rimelq/VISTAF-RoboSkin-Vision-Integrated-Multimodal-Sensor/Multimodal_Sensor/Demos_report/FINAL_E_deformed/combined_outputs/temp_temperature_legend_horizontal.png

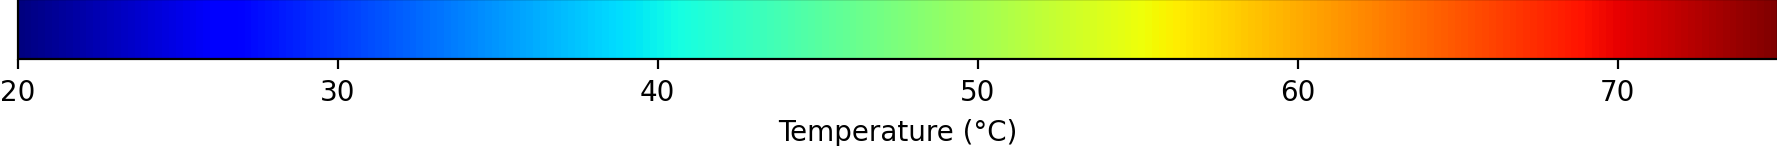
Multimodal_Sensor/Demos_report/FINAL_E_deformed/combined_outputs/temp_temperature_legend_horizontal.png
