rimelq/VISTAF-RoboSkin-Vision-Integrated-Multimodal-Sensor/Multimodal_Sensor/Demos_report/FINAL_E_deformed/force_sensing/ftp_run/03_ref_def_crops_with_roi.png

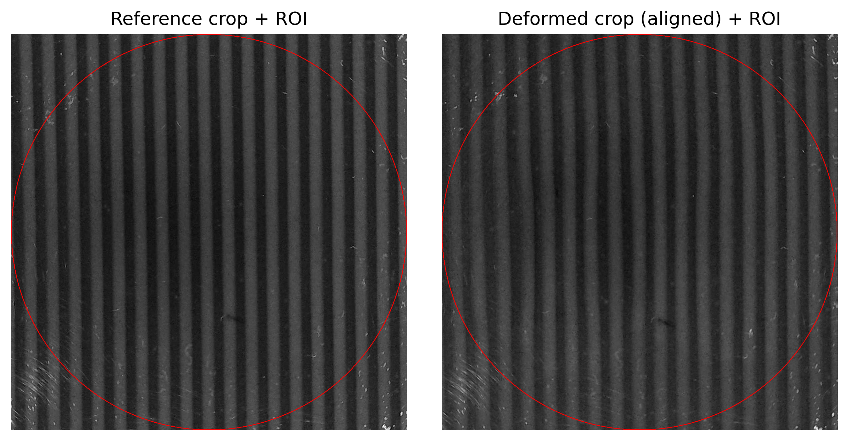
Multimodal_Sensor/Demos_report/FINAL_E_deformed/force_sensing/ftp_run/03_ref_def_crops_with_roi.png
