rimelq/VISTAF-RoboSkin-Vision-Integrated-Multimodal-Sensor/Multimodal_Sensor/Demos_report/FINAL_E_deformed/temperature_sensing/mask_color_support.png

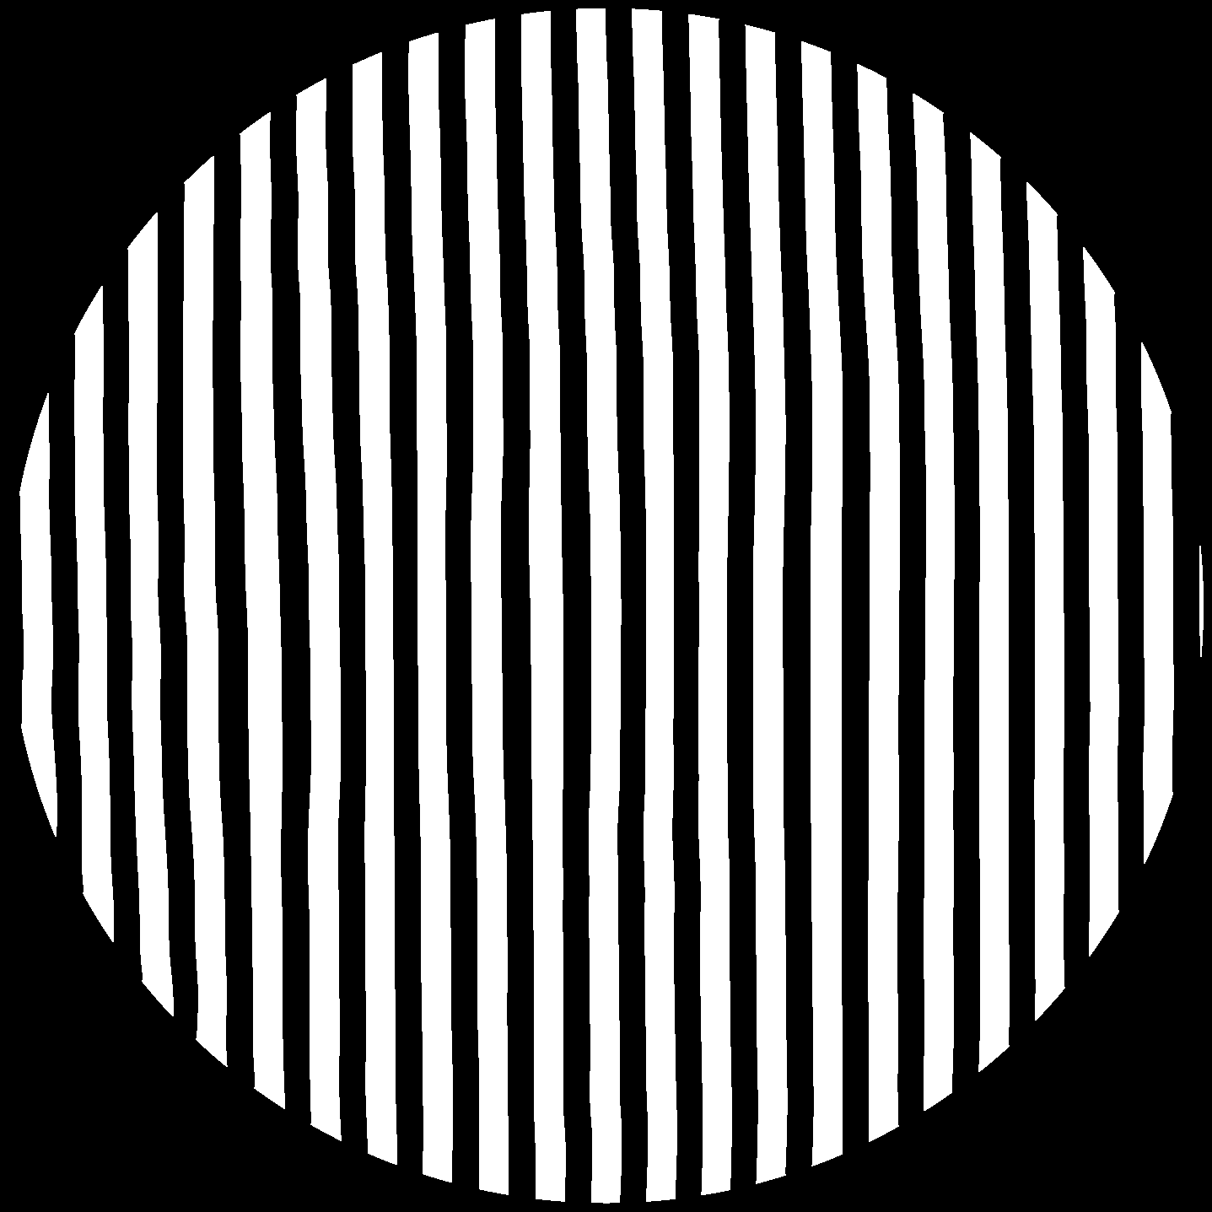
Multimodal_Sensor/Demos_report/FINAL_E_deformed/temperature_sensing/mask_color_support.png
