rimelq/VISTAF-RoboSkin-Vision-Integrated-Multimodal-Sensor/Multimodal_Sensor/Demos_report/FINAL_E_deformed/temperature_sensing/mask_roi.png

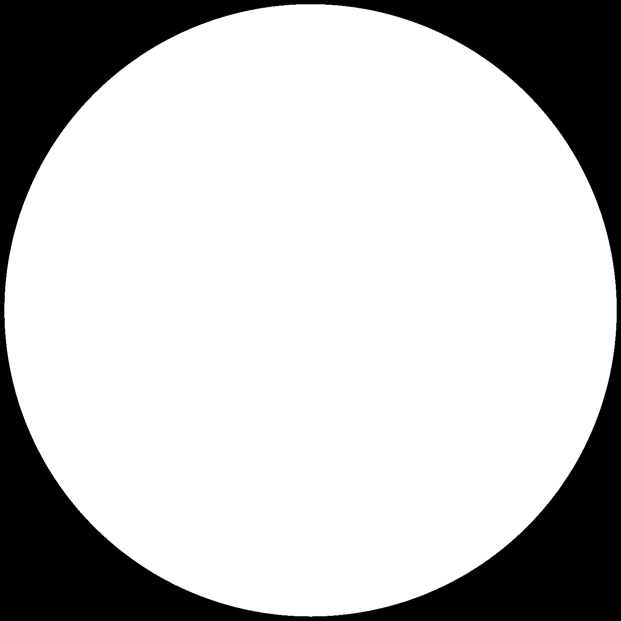
Multimodal_Sensor/Demos_report/FINAL_E_deformed/temperature_sensing/mask_roi.png
