rimelq/VISTAF-RoboSkin-Vision-Integrated-Multimodal-Sensor/Multimodal_Sensor/Demos_report/FINAL_F_deformed/force_sensing/ftp_run/07_phase_and_height_FINAL_SMOOTH_ROI.png

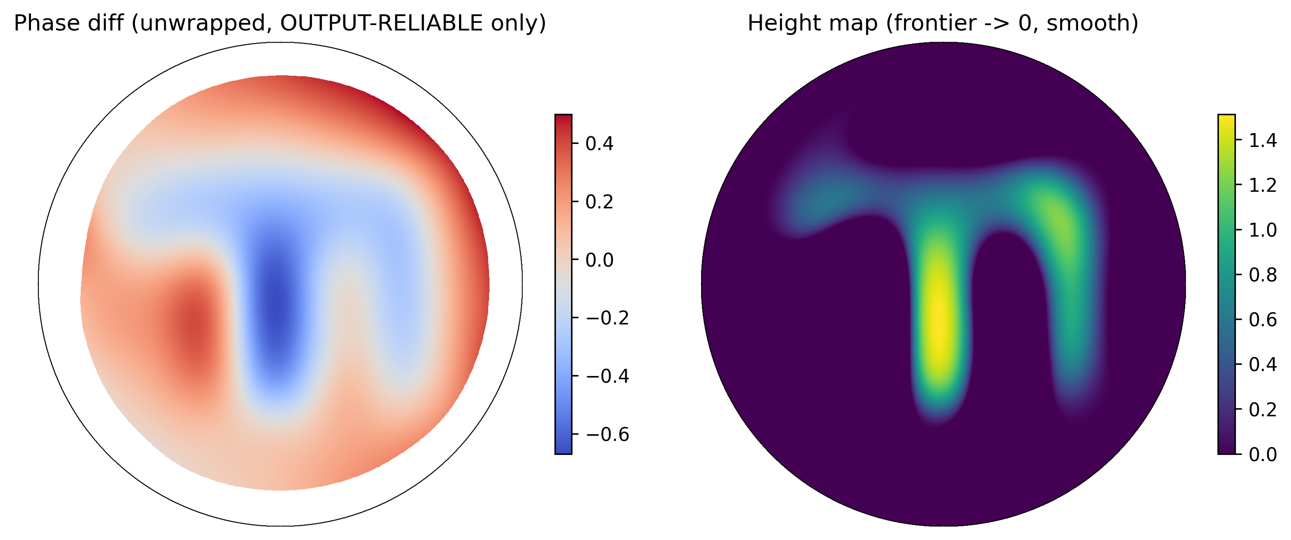
Multimodal_Sensor/Demos_report/FINAL_F_deformed/force_sensing/ftp_run/07_phase_and_height_FINAL_SMOOTH_ROI.png
