rimelq/VISTAF-RoboSkin-Vision-Integrated-Multimodal-Sensor/Multimodal_Sensor/Demos_report/FINAL_P_deformed/temperature_sensing/mask_dark.png

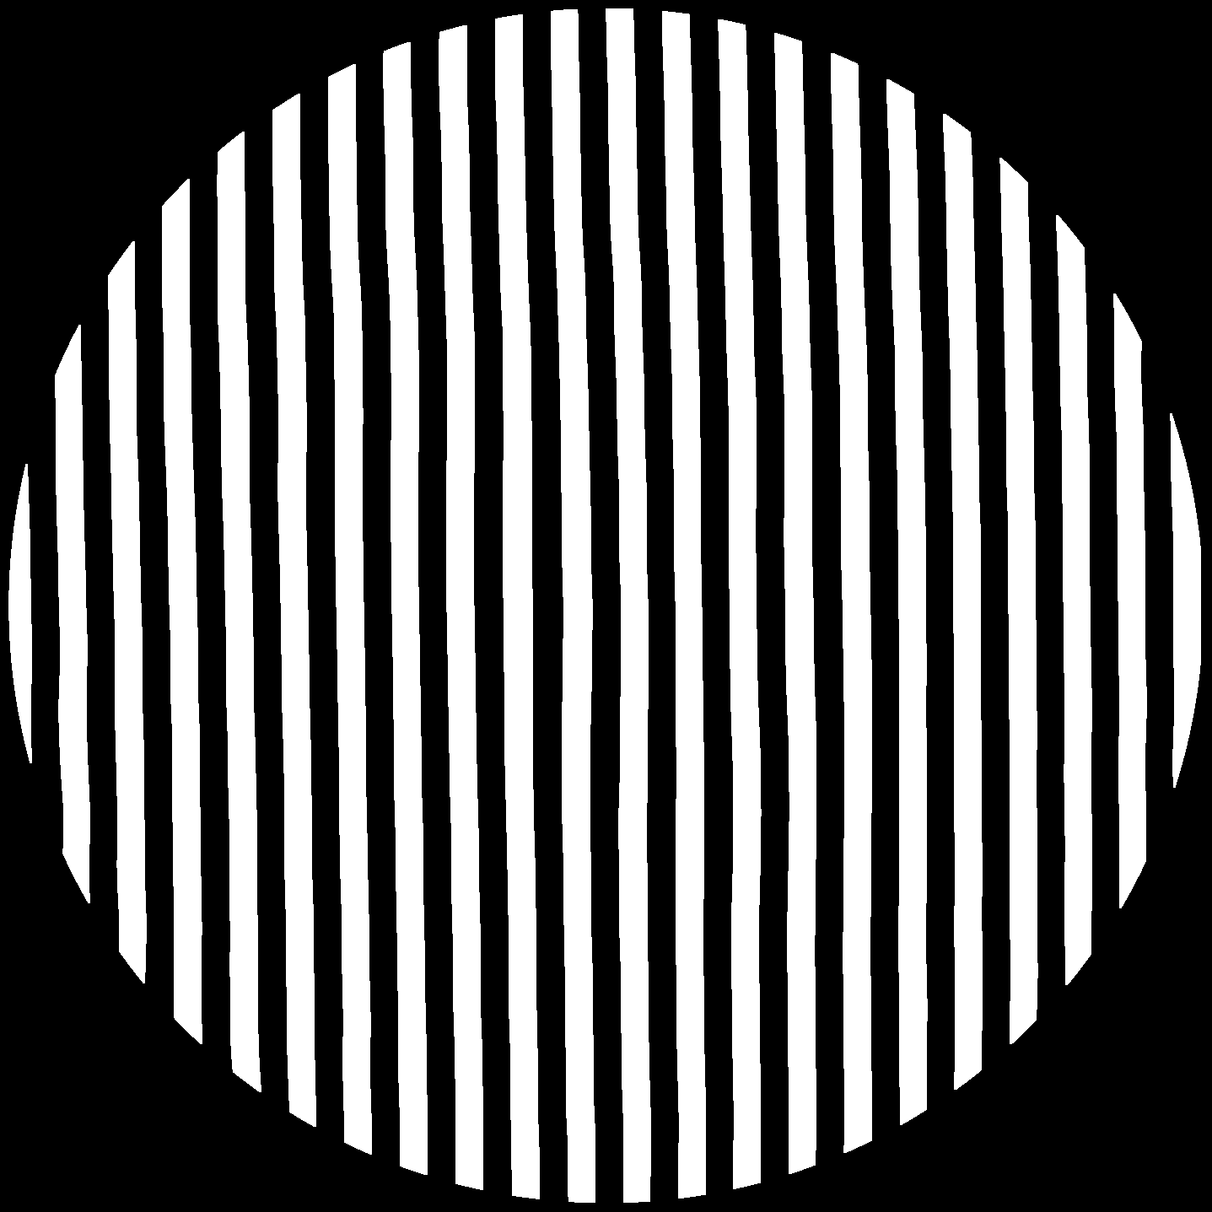
Multimodal_Sensor/Demos_report/FINAL_P_deformed/temperature_sensing/mask_dark.png
