rimelq/VISTAF-RoboSkin-Vision-Integrated-Multimodal-Sensor/Multimodal_Sensor/Demos_report/FINAL_ROUND_METAL/combined_outputs/temp_temperature_map_final_colormap.png

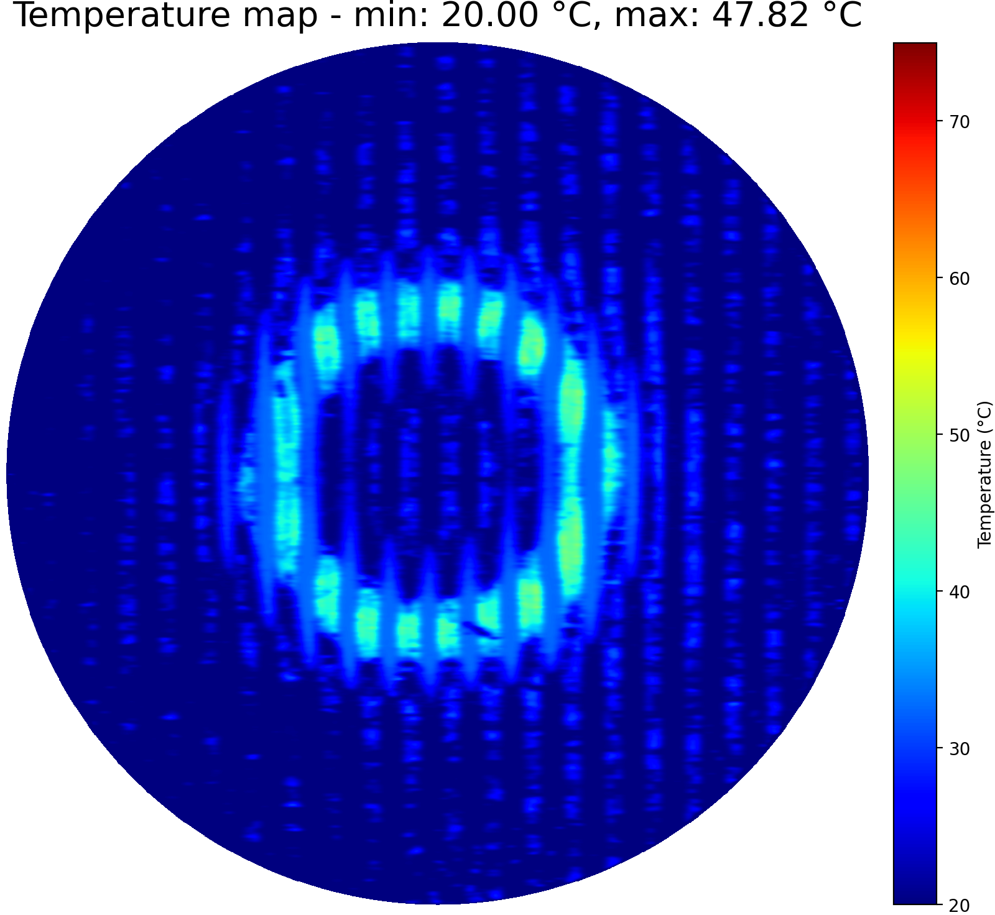
Multimodal_Sensor/Demos_report/FINAL_ROUND_METAL/combined_outputs/temp_temperature_map_final_colormap.png
