rimelq/VISTAF-RoboSkin-Vision-Integrated-Multimodal-Sensor/Multimodal_Sensor/Demos_report/FINAL_ROUND_METAL/temperature_sensing/mask_color_ok.png

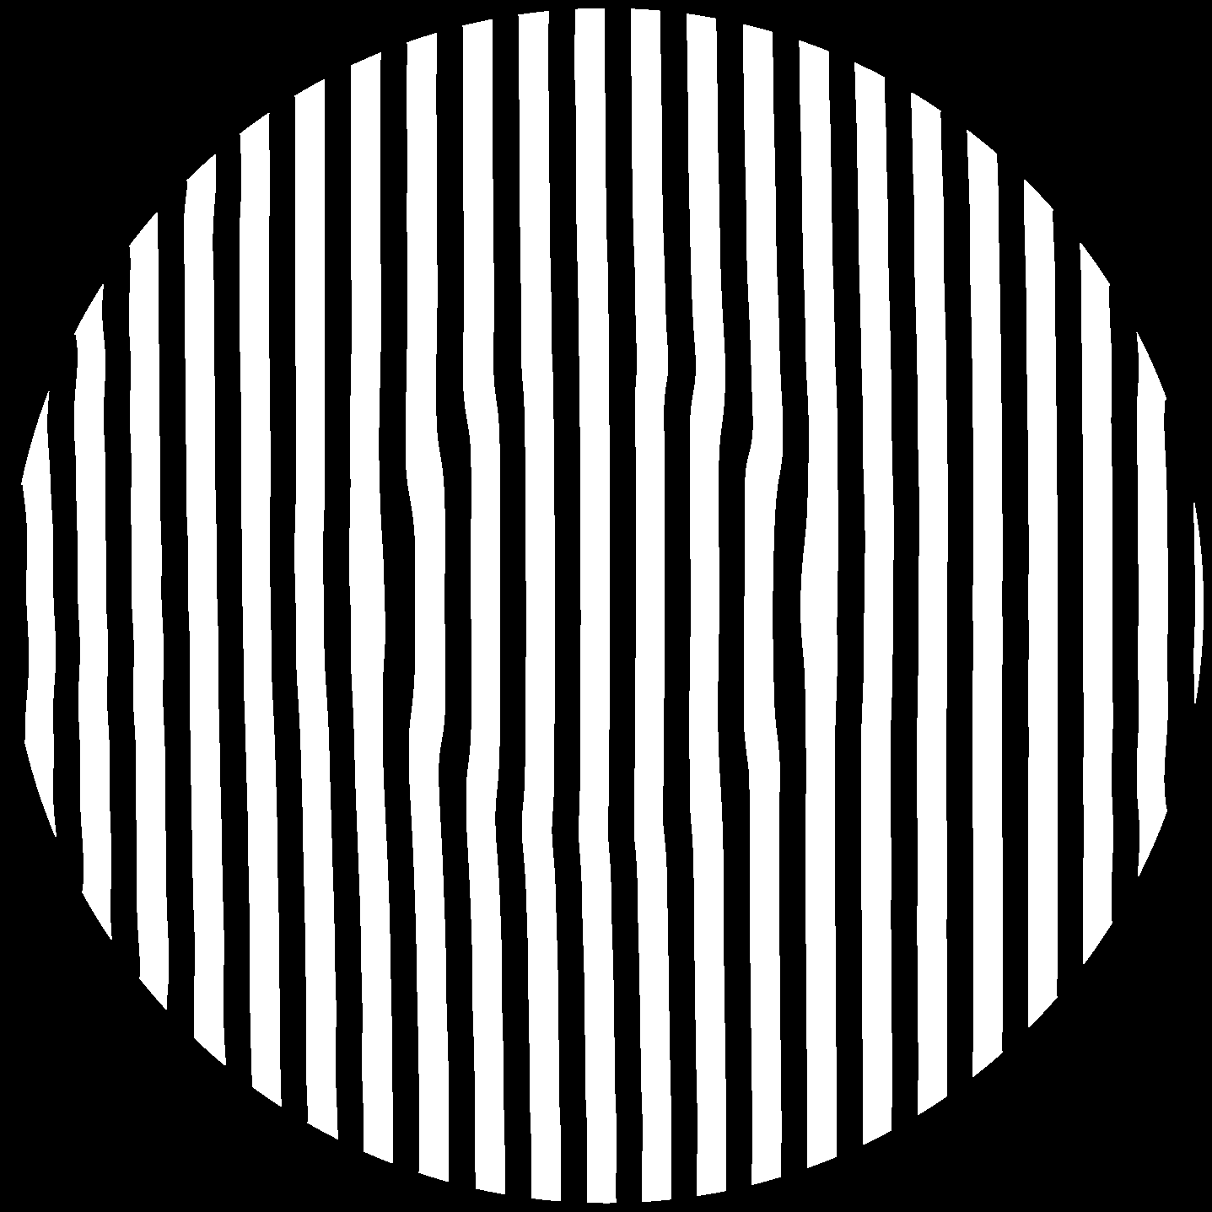
Multimodal_Sensor/Demos_report/FINAL_ROUND_METAL/temperature_sensing/mask_color_ok.png
