rimelq/VISTAF-RoboSkin-Vision-Integrated-Multimodal-Sensor/Multimodal_Sensor/Demos_report/FINAL_ROUND_METAL/temperature_sensing/temperature_map_final_colormap_overlay.png

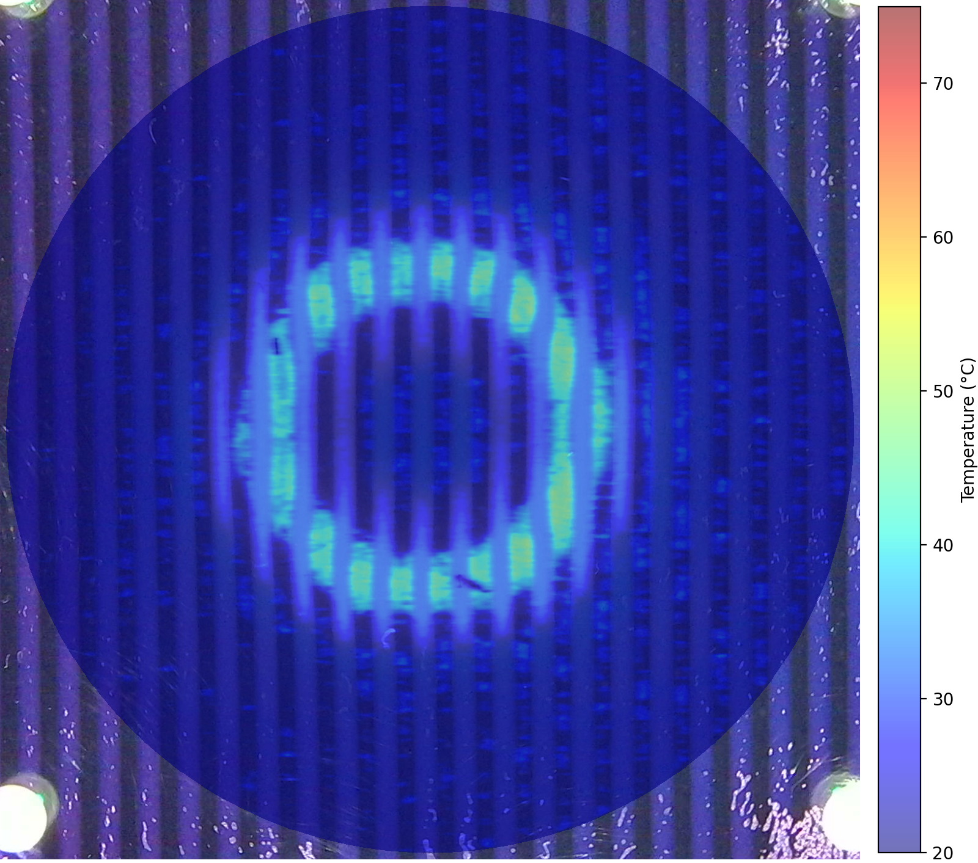
Multimodal_Sensor/Demos_report/FINAL_ROUND_METAL/temperature_sensing/temperature_map_final_colormap_overlay.png
