rimelq/VISTAF-RoboSkin-Vision-Integrated-Multimodal-Sensor/Multimodal_Sensor/Demos_report/FINAL_TEMP_DEMO/combined_outputs/force_shape_heightmap.png

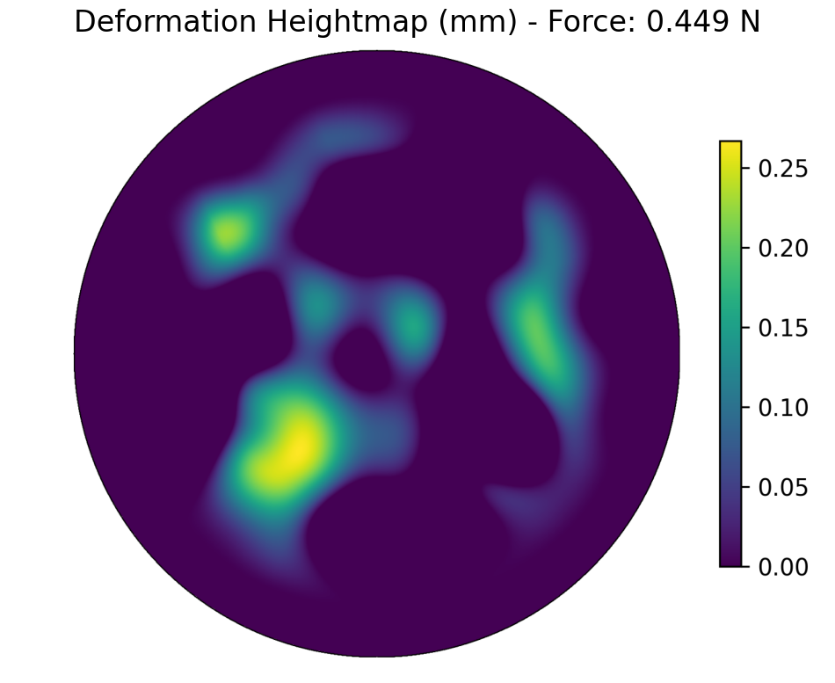
Multimodal_Sensor/Demos_report/FINAL_TEMP_DEMO/combined_outputs/force_shape_heightmap.png
