rimelq/VISTAF-RoboSkin-Vision-Integrated-Multimodal-Sensor/Multimodal_Sensor/Demos_report/FINAL_TEMP_DEMO/combined_outputs/temp_temperature_map_final_colormap_overlay.png

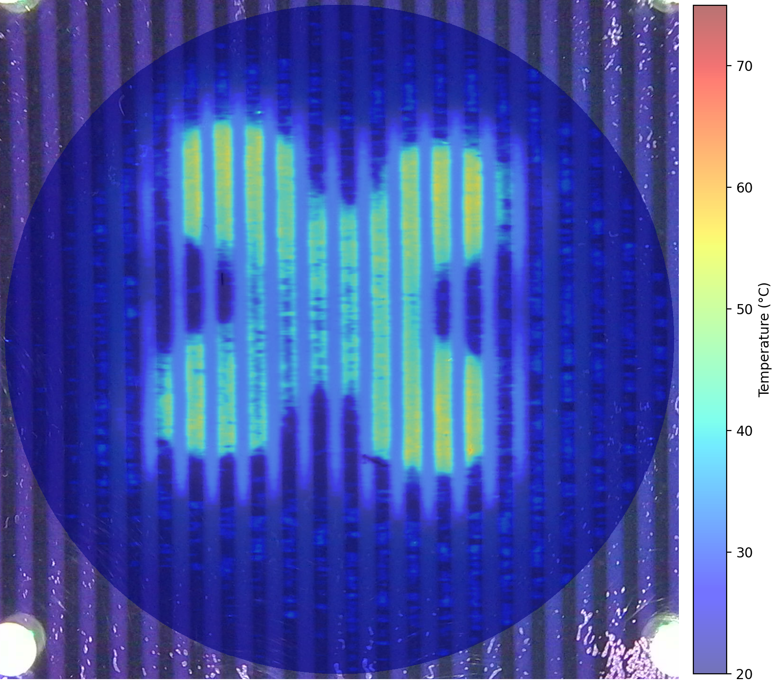
Multimodal_Sensor/Demos_report/FINAL_TEMP_DEMO/combined_outputs/temp_temperature_map_final_colormap_overlay.png
