rimelq/VISTAF-RoboSkin-Vision-Integrated-Multimodal-Sensor/Multimodal_Sensor/Demos_report/FINAL_TEMP_DEMO/temperature_sensing/temperature_map_final_colormap.png

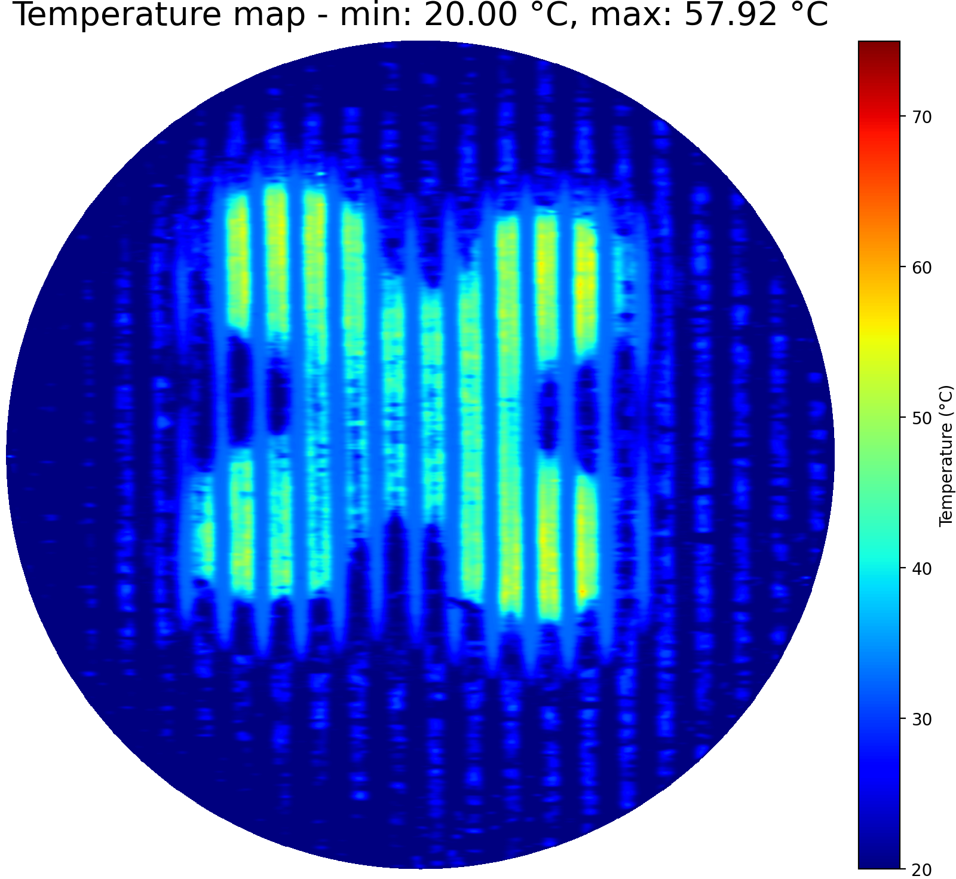
Multimodal_Sensor/Demos_report/FINAL_TEMP_DEMO/temperature_sensing/temperature_map_final_colormap.png
