rimelq/VISTAF-RoboSkin-Vision-Integrated-Multimodal-Sensor/Force/Height_to_force/calibration_out/force_vs_volume_fit.png

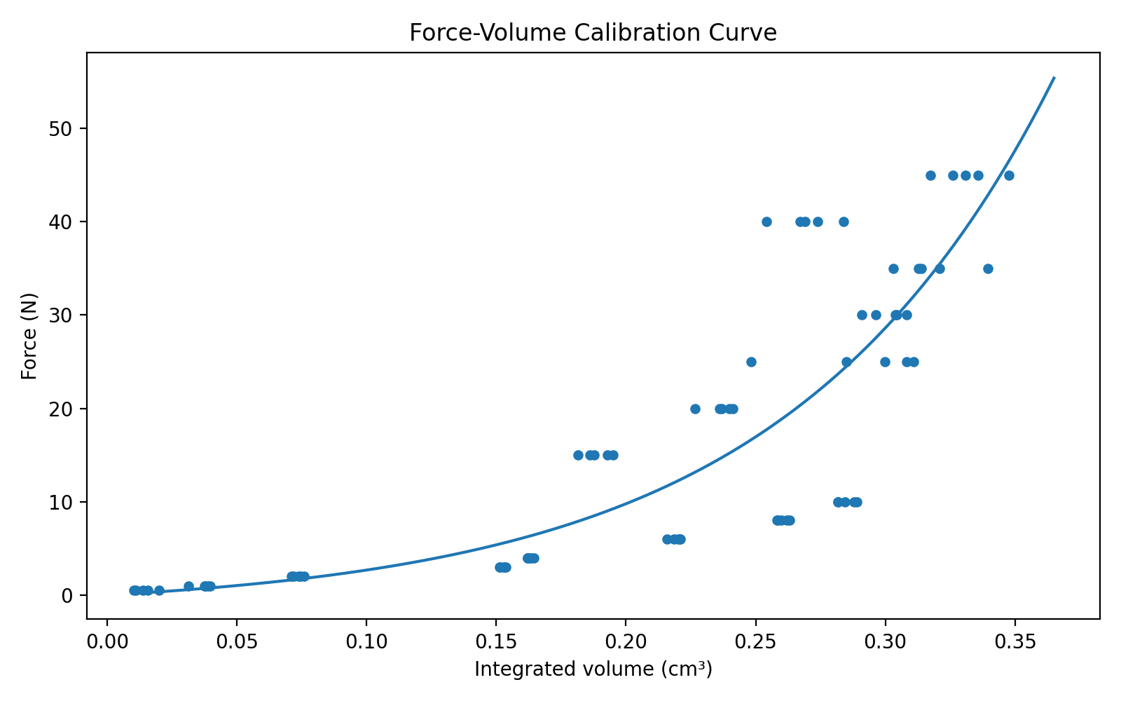
Force/Height_to_force/calibration_out/force_vs_volume_fit.png
