rimelq/VISTAF-RoboSkin-Vision-Integrated-Multimodal-Sensor/Force/Height_to_force/calibration_out/ftp_runs/003_sphere-3_F0.5N/07_phase_and_height_FINAL_SMOOTH_ROI.png

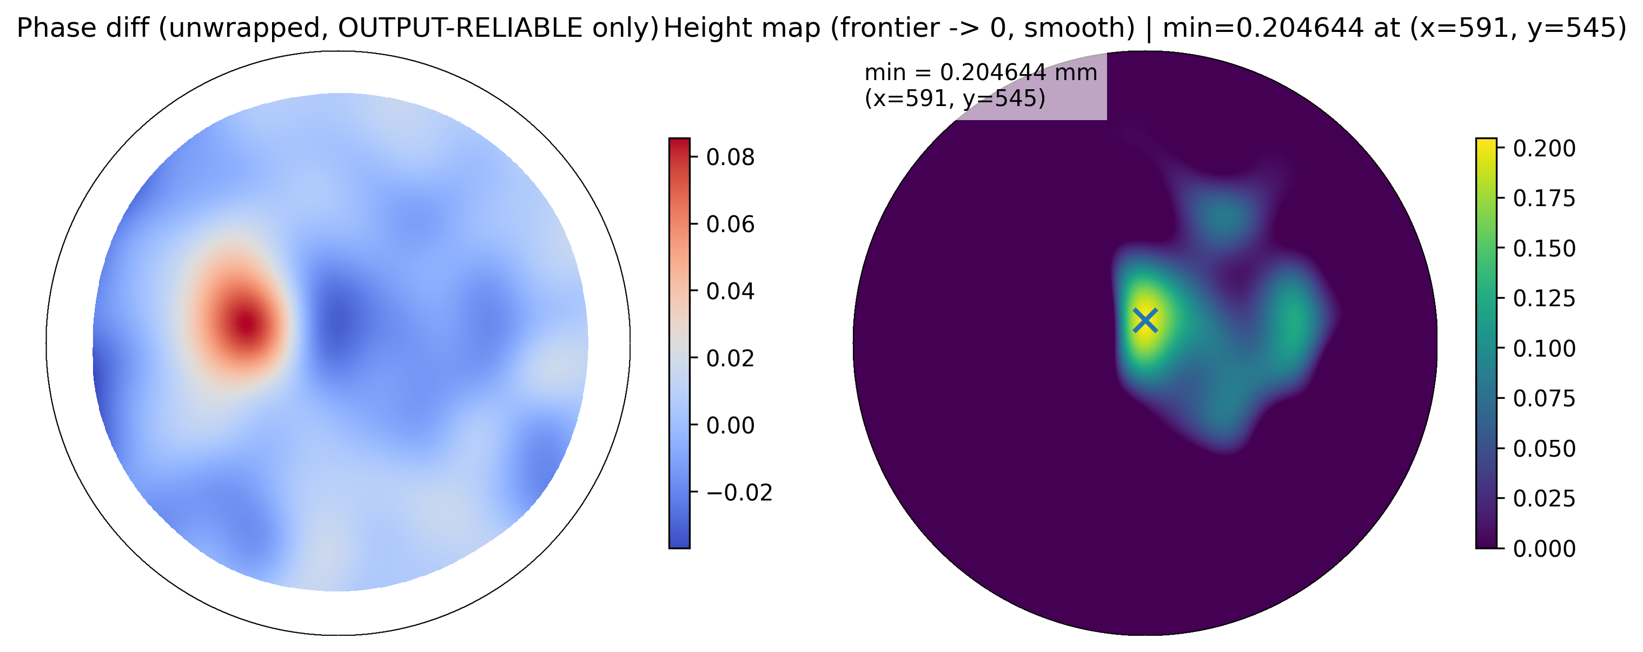
Force/Height_to_force/calibration_out/ftp_runs/003_sphere-3_F0.5N/07_phase_and_height_FINAL_SMOOTH_ROI.png
