rimelq/VISTAF-RoboSkin-Vision-Integrated-Multimodal-Sensor/Force/Height_to_force/calibration_out/ftp_runs/021_sphere-21_F4N/07_phase_and_height_FINAL_SMOOTH_ROI.png

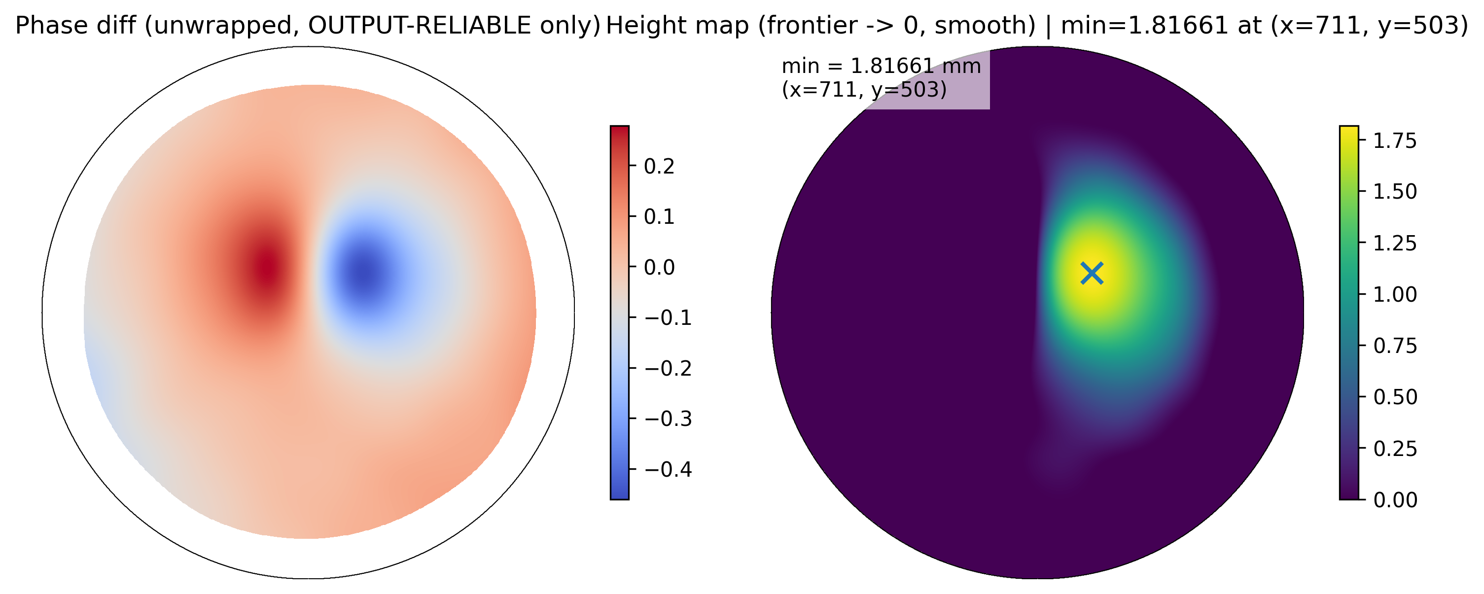
Force/Height_to_force/calibration_out/ftp_runs/021_sphere-21_F4N/07_phase_and_height_FINAL_SMOOTH_ROI.png
