rimelq/VISTAF-RoboSkin-Vision-Integrated-Multimodal-Sensor/Force/Height_to_force/calibration_out/ftp_runs/028_sphere-28_F6N/03_ref_def_crops_with_roi.png

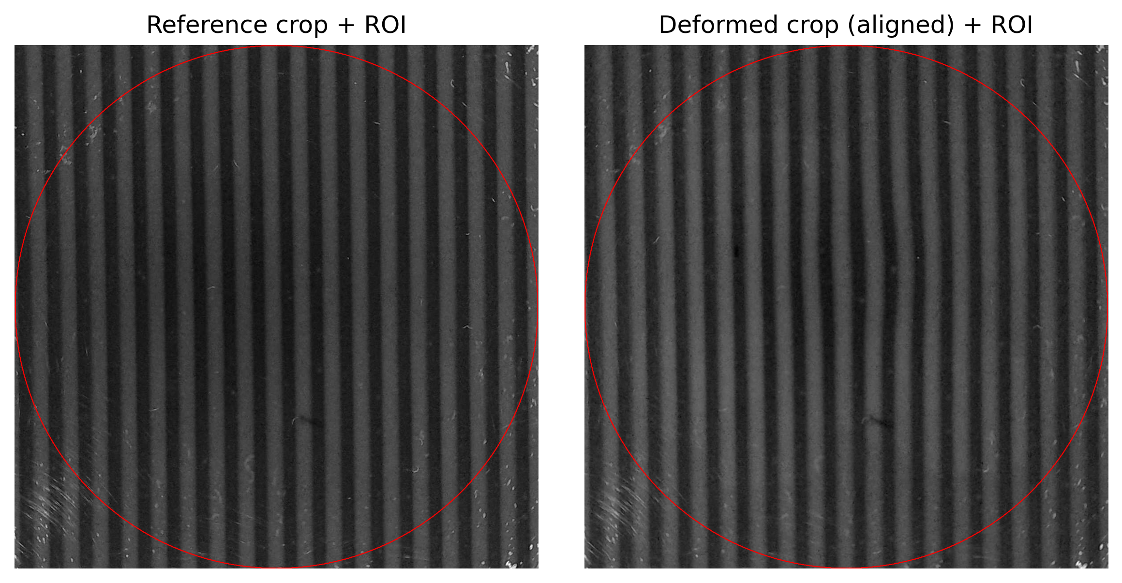
Force/Height_to_force/calibration_out/ftp_runs/028_sphere-28_F6N/03_ref_def_crops_with_roi.png
