rimelq/VISTAF-RoboSkin-Vision-Integrated-Multimodal-Sensor/Force/Phase_to_height/calibration_out/calibration_plot.png

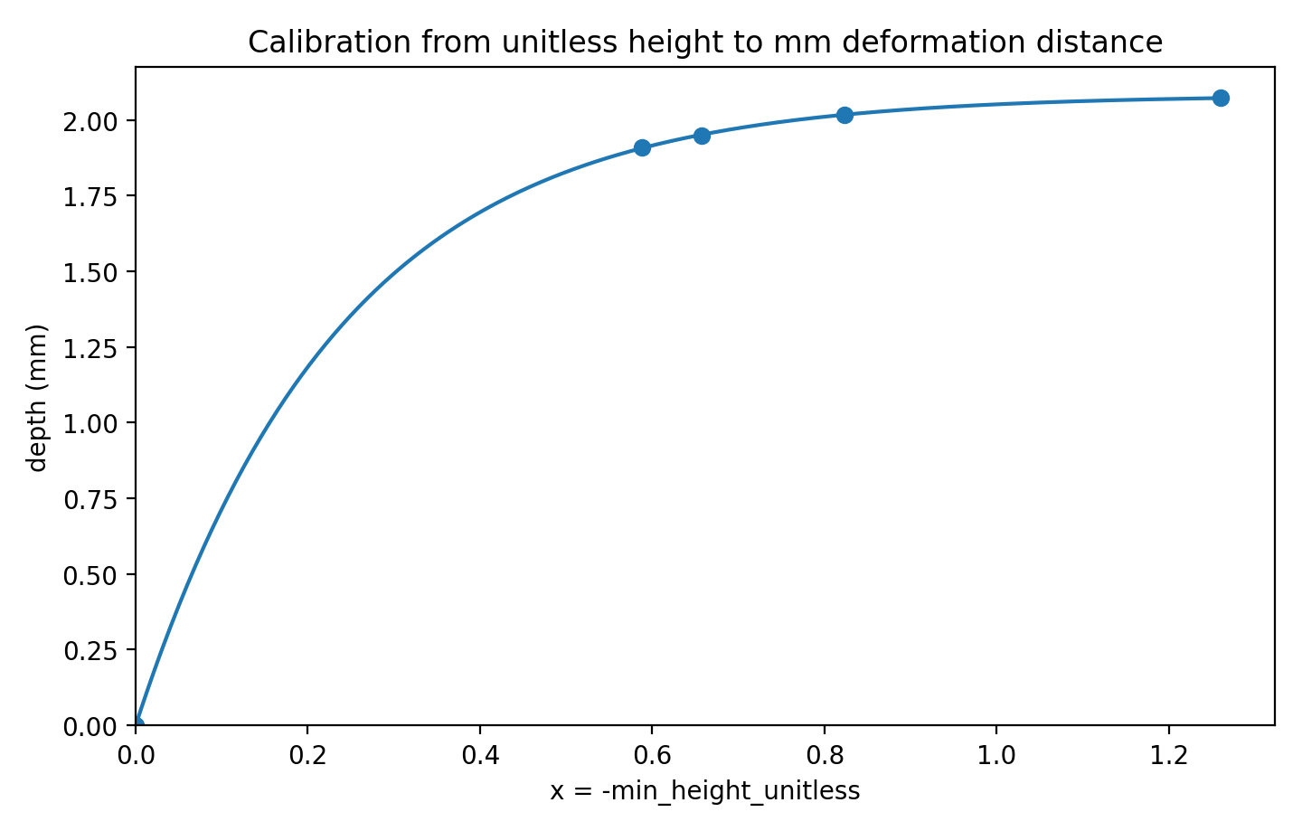
Force/Phase_to_height/calibration_out/calibration_plot.png
