rimelq/VISTAF-RoboSkin-Vision-Integrated-Multimodal-Sensor/Force/Phase_to_height/calibration_out/Height_1mm_deformed/heightmap.png

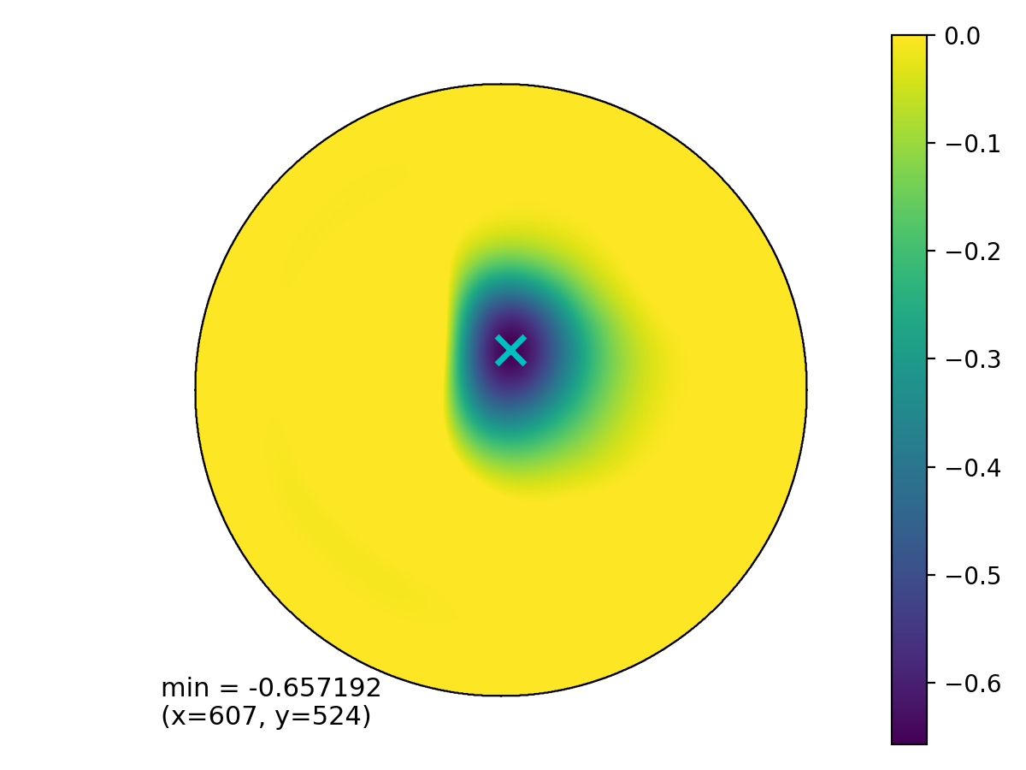
Force/Phase_to_height/calibration_out/Height_1mm_deformed/heightmap.png
