rimelq/VISTAF-RoboSkin-Vision-Integrated-Multimodal-Sensor/Temperature/Colored_Model/calibration_out/00_roi_overlay.png

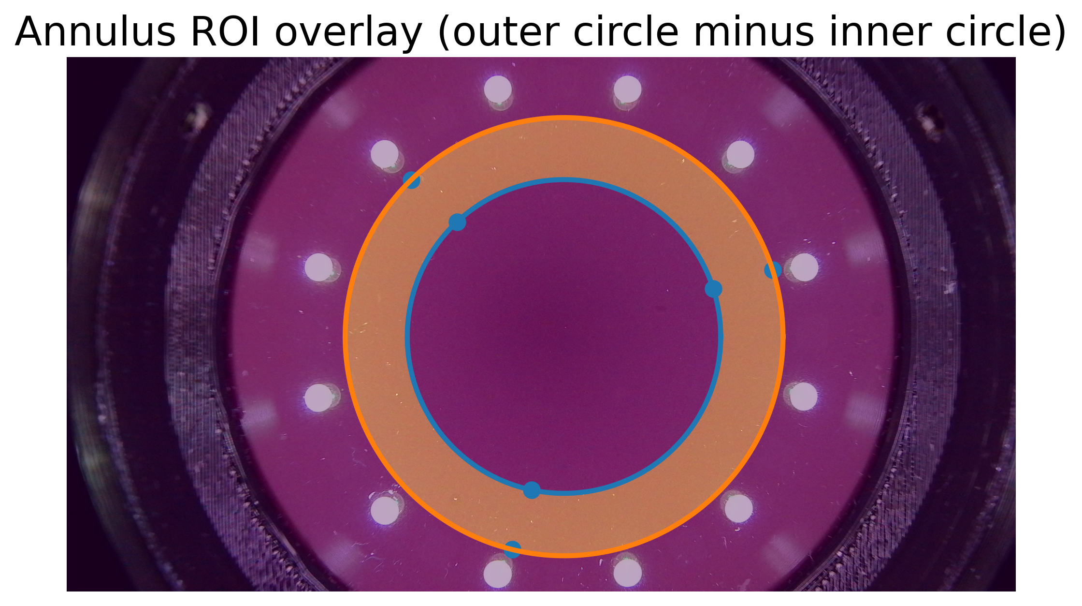
Temperature/Colored_Model/calibration_out/00_roi_overlay.png
