rimelq/VISTAF-RoboSkin-Vision-Integrated-Multimodal-Sensor/Temperature/Colored_Model/calibration_out/03_hysteresis_L_vs_T_models.png

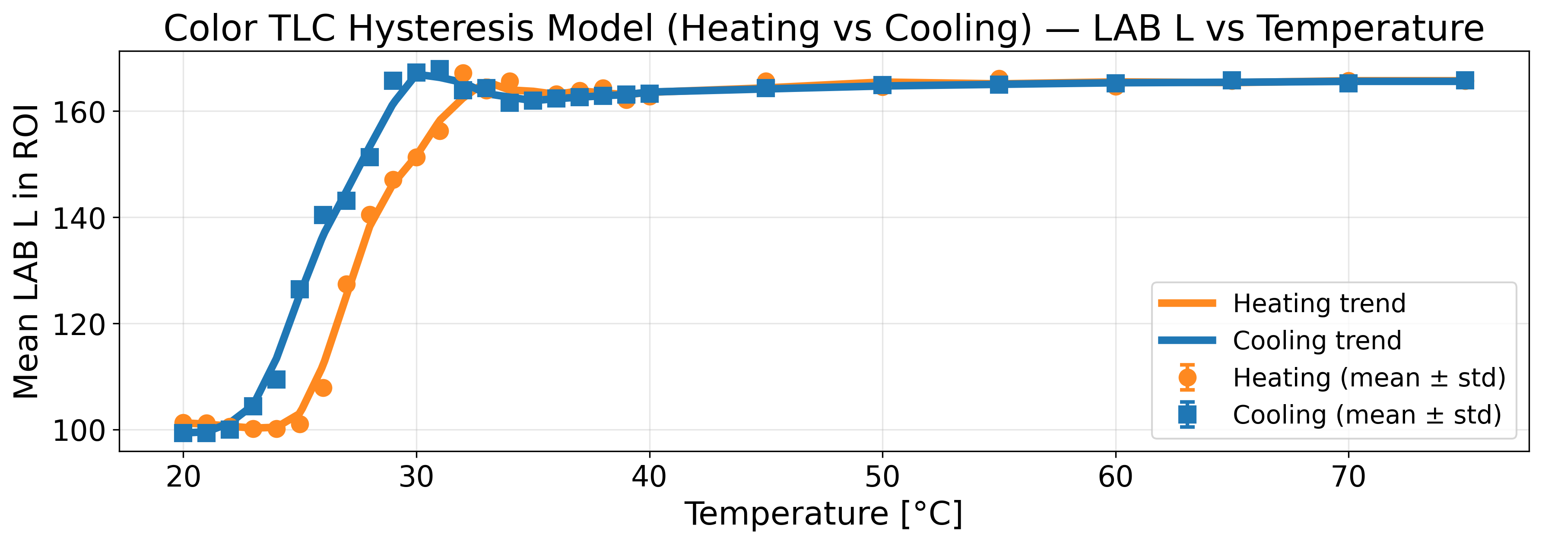
Temperature/Colored_Model/calibration_out/03_hysteresis_L_vs_T_models.png
