rimelq/VISTAF-RoboSkin-Vision-Integrated-Multimodal-Sensor/Temperature/Colored_Model/calibration_out/06_global_L_vs_T_all_trend.png

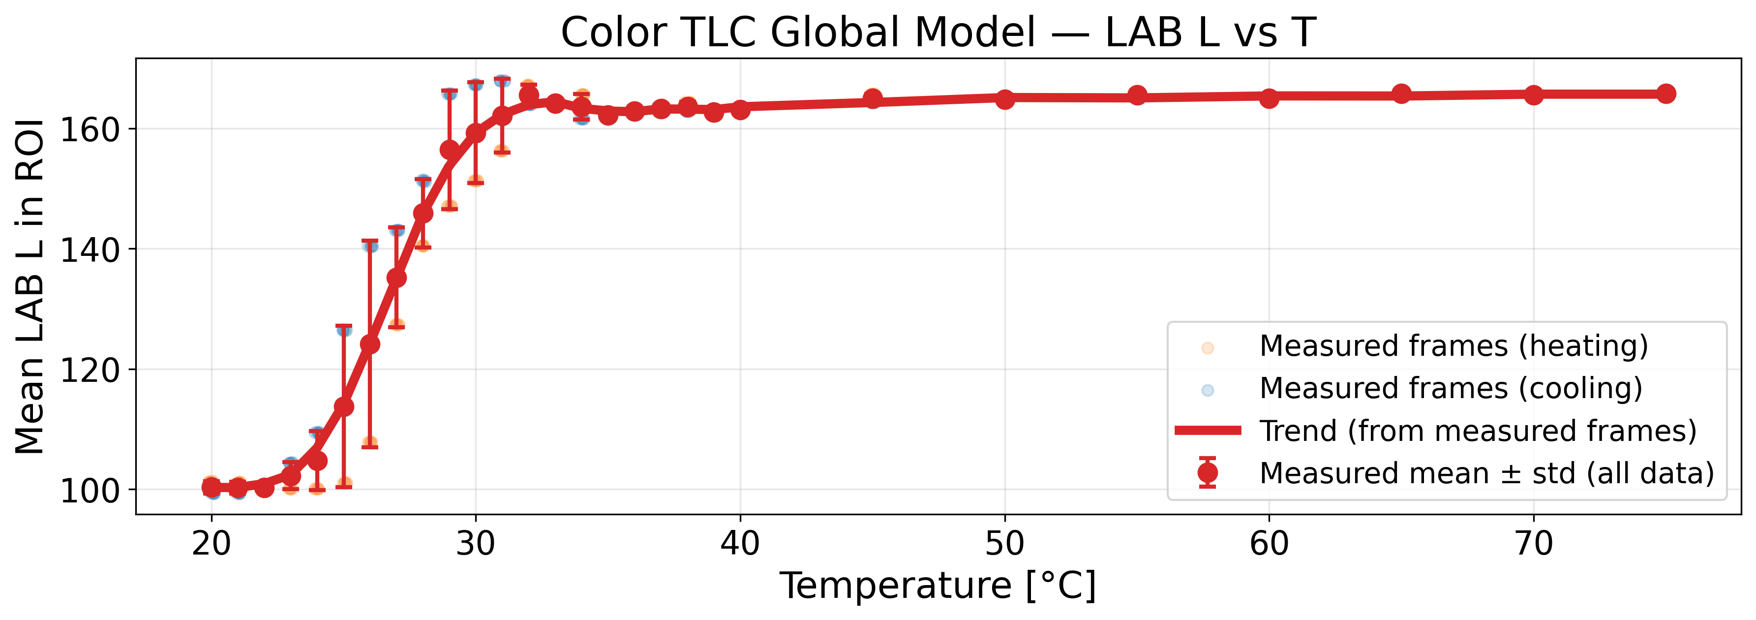
Temperature/Colored_Model/calibration_out/06_global_L_vs_T_all_trend.png
