rimelq/VISTAF-RoboSkin-Vision-Integrated-Multimodal-Sensor/Temperature/Colored_Model/calibration_out/08_global_mae_vs_T.png

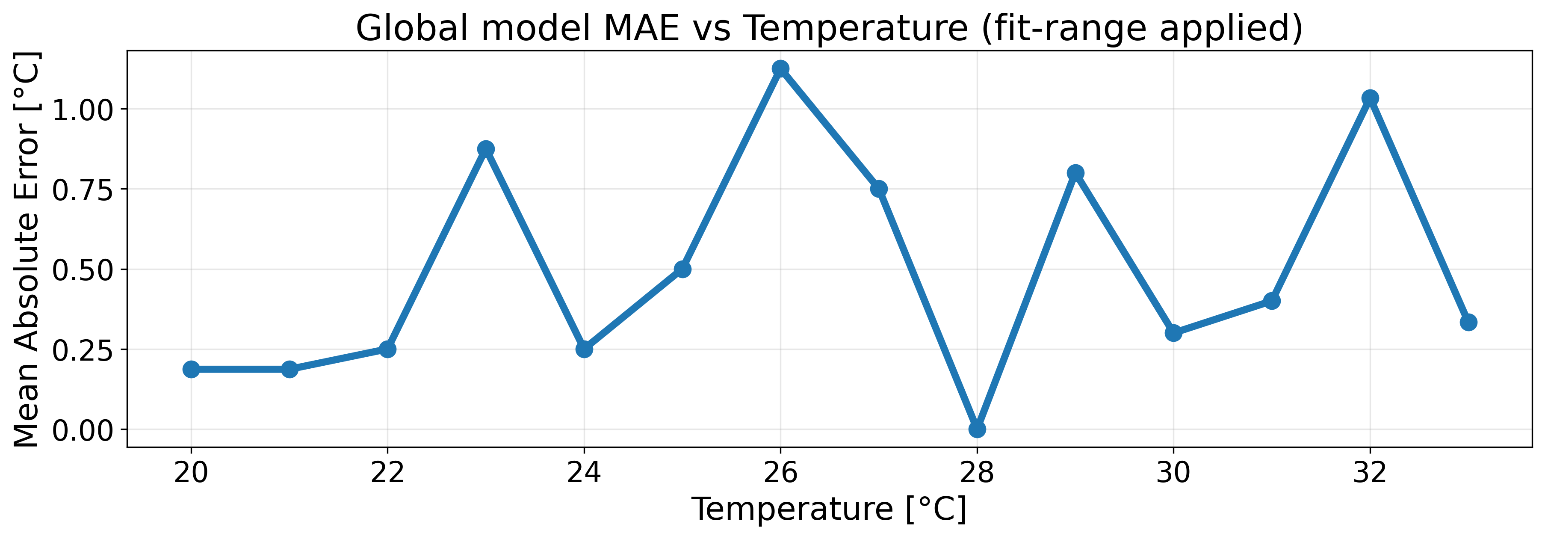
Temperature/Colored_Model/calibration_out/08_global_mae_vs_T.png
