rimelq/VISTAF-RoboSkin-Vision-Integrated-Multimodal-Sensor/Temperature/MixedColorBlack_Model/calibration_out/01_heating_gray_vs_T_modelcurve.png

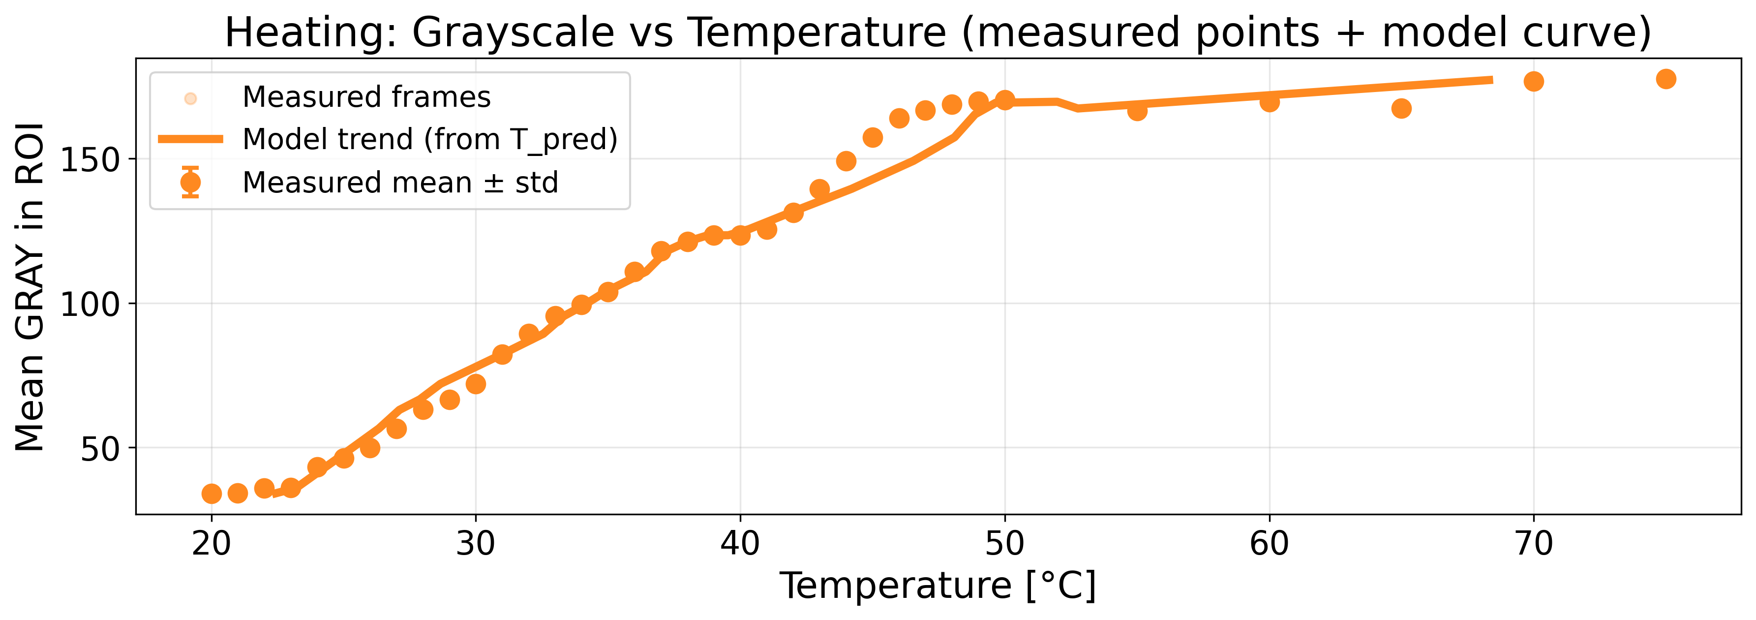
Temperature/MixedColorBlack_Model/calibration_out/01_heating_gray_vs_T_modelcurve.png
