rimelq/VISTAF-RoboSkin-Vision-Integrated-Multimodal-Sensor/Temperature/MixedColorBlack_Model/calibration_out/05_global_true_vs_pred.png

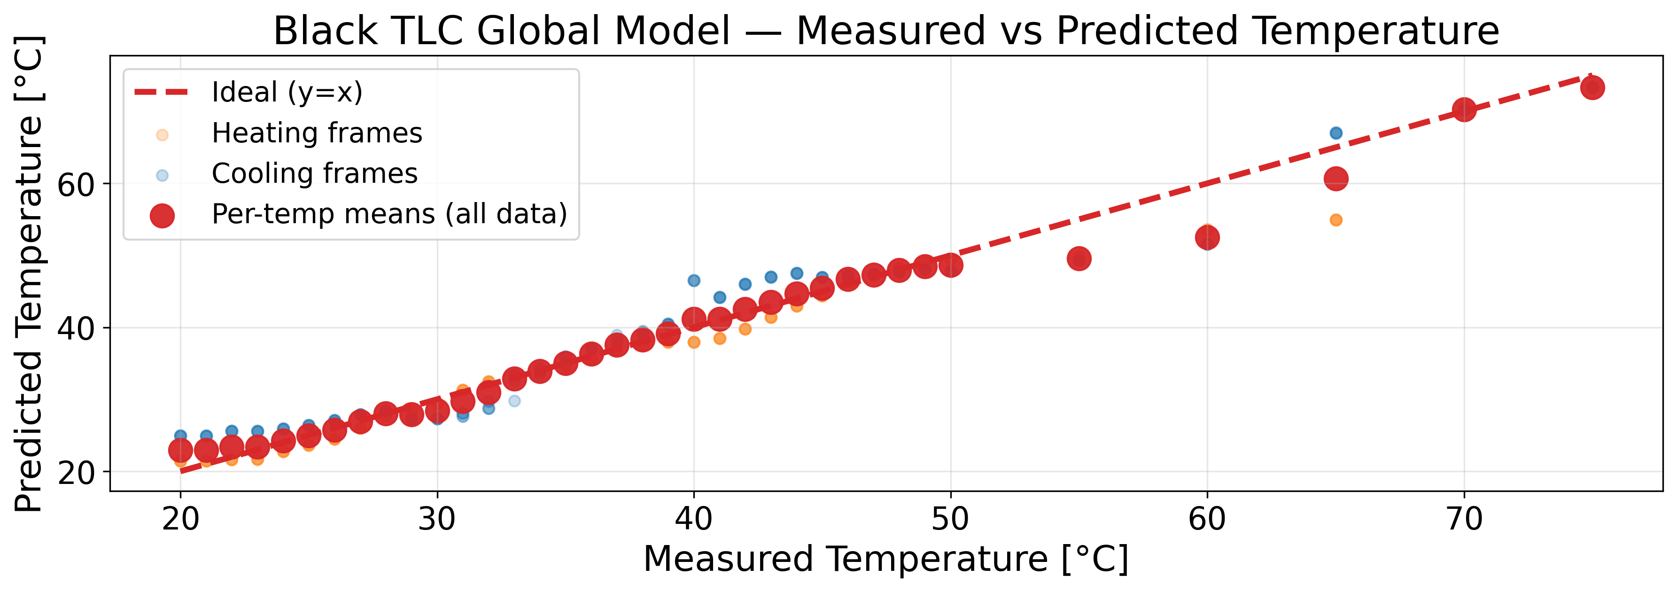
Temperature/MixedColorBlack_Model/calibration_out/05_global_true_vs_pred.png
