rimelq/VISTAF-RoboSkin-Vision-Integrated-Multimodal-Sensor/Temperature/MixedColorBlack_Model/calibration_out/06_global_gray_vs_T_all_modelcurve.png

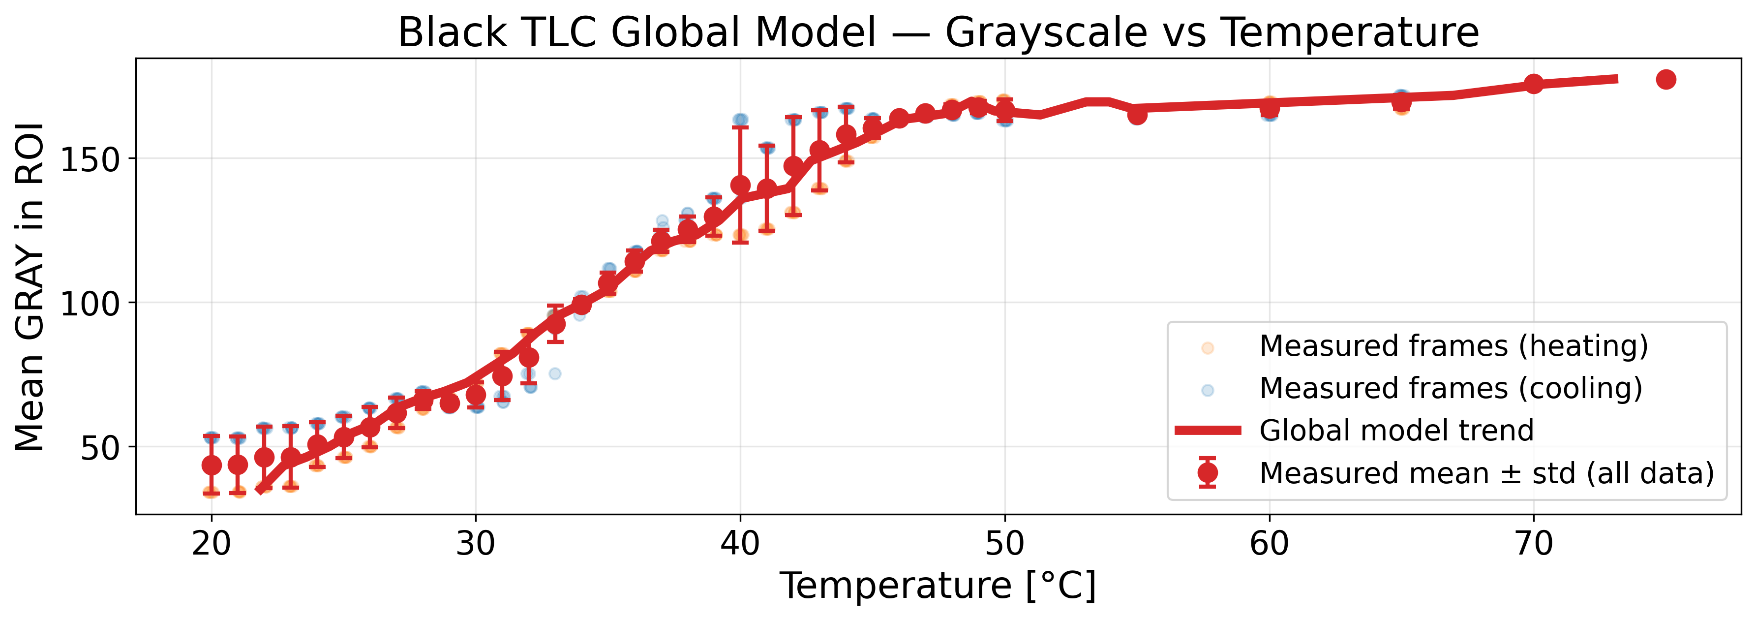
Temperature/MixedColorBlack_Model/calibration_out/06_global_gray_vs_T_all_modelcurve.png
