rimelq/VISTAF-RoboSkin-Vision-Integrated-Multimodal-Sensor/Force/force_sensor_out/ftp_run/05_fft_debug_panels.png

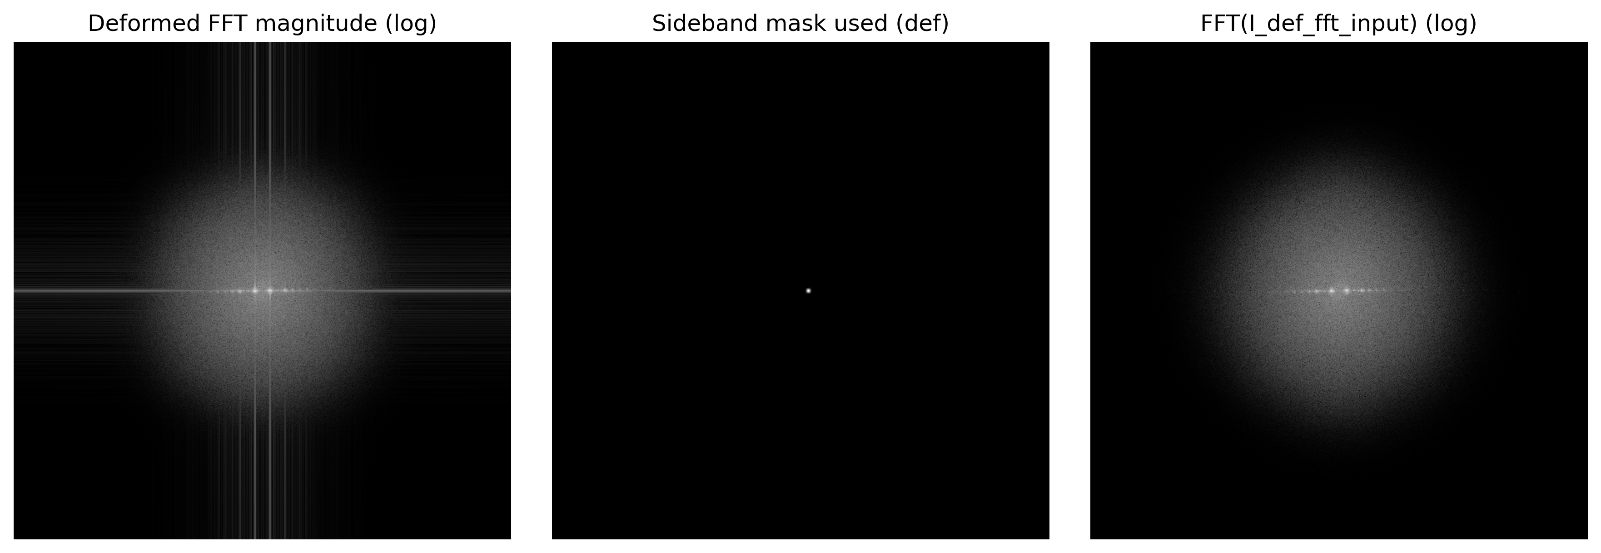
Force/force_sensor_out/ftp_run/05_fft_debug_panels.png
