rimelq/VISTAF-RoboSkin-Vision-Integrated-Multimodal-Sensor/Force/force_sensor_out/ftp_run/DEBUG_ramp_phase_diff.png

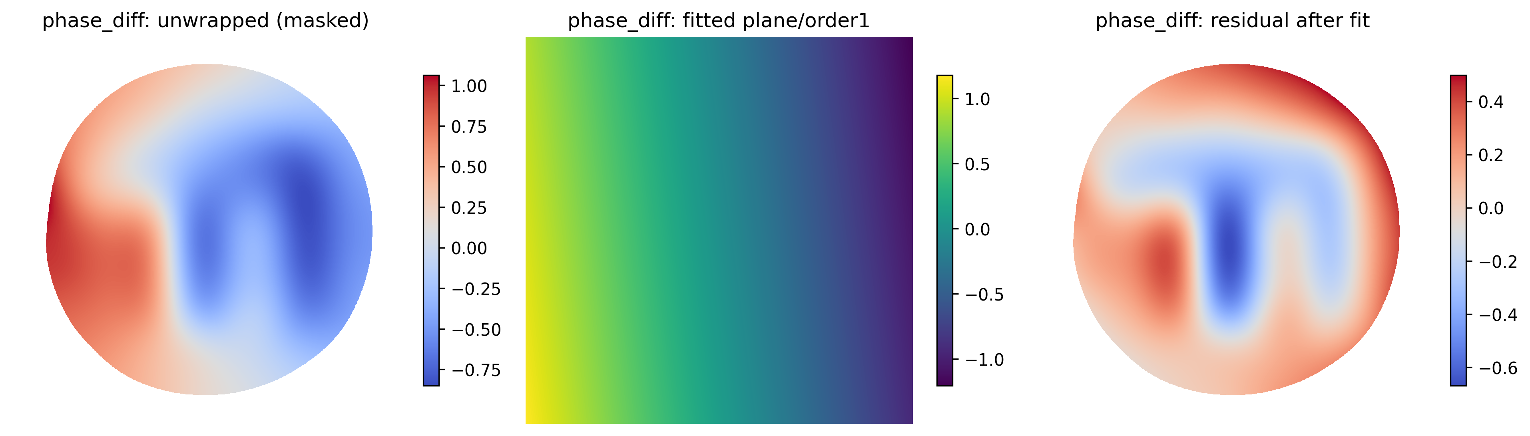
Force/force_sensor_out/ftp_run/DEBUG_ramp_phase_diff.png
