rimelq/VISTAF-RoboSkin-Vision-Integrated-Multimodal-Sensor/Force/Height_to_force/calibration_out/ftp_runs/002_sphere-2_F0.5N/DEBUG_ramp_cross_phase_diff.png

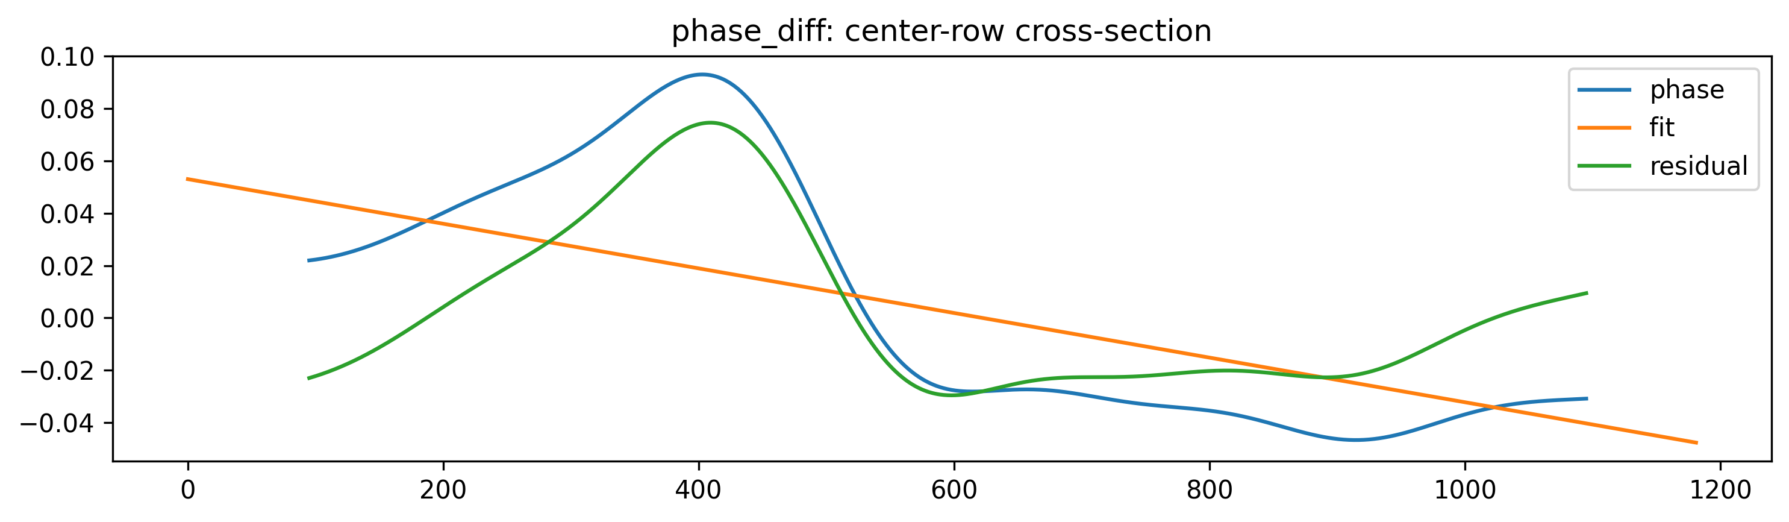
Force/Height_to_force/calibration_out/ftp_runs/002_sphere-2_F0.5N/DEBUG_ramp_cross_phase_diff.png
