rimelq/VISTAF-RoboSkin-Vision-Integrated-Multimodal-Sensor/Force/Height_to_force/calibration_out/ftp_runs/006_sphere-6_F1N/DEBUG_ramp_cross_phase_diff.png

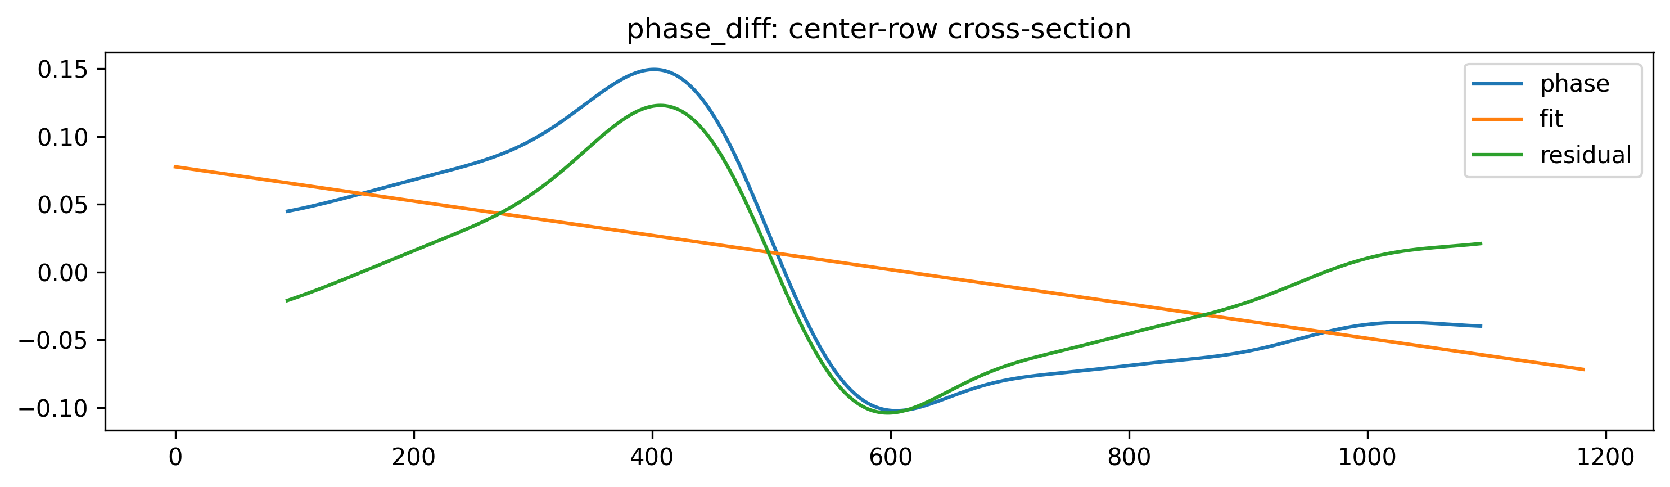
Force/Height_to_force/calibration_out/ftp_runs/006_sphere-6_F1N/DEBUG_ramp_cross_phase_diff.png
