rimelq/VISTAF-RoboSkin-Vision-Integrated-Multimodal-Sensor/Force/Height_to_force/calibration_out/ftp_runs/026_sphere-26_F6N/DEBUG_ramp_phase_diff.png

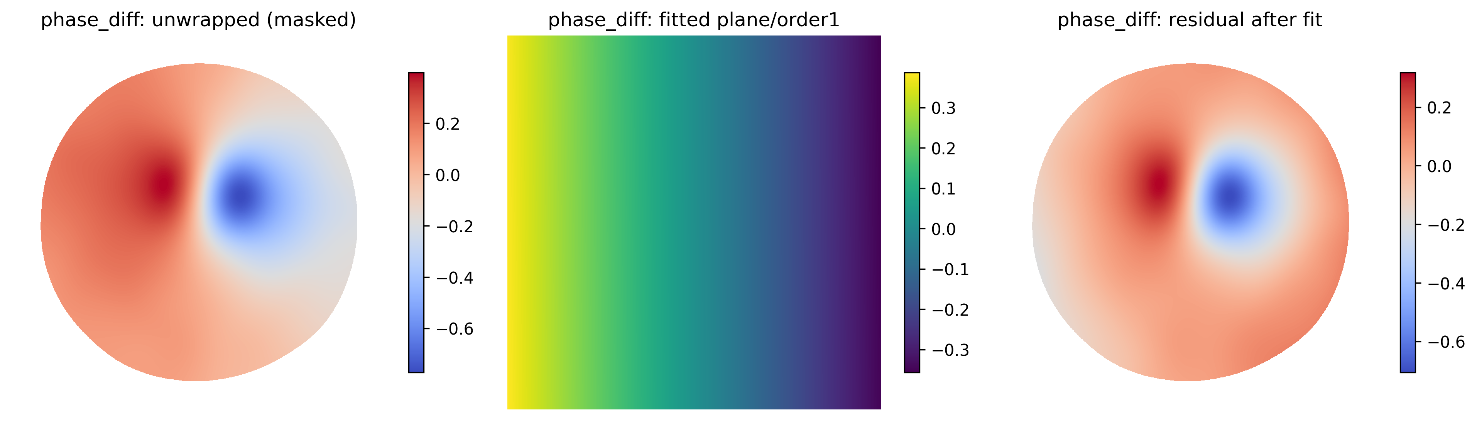
Force/Height_to_force/calibration_out/ftp_runs/026_sphere-26_F6N/DEBUG_ramp_phase_diff.png
