rimelq/VISTAF-RoboSkin-Vision-Integrated-Multimodal-Sensor/Multimodal_Sensor/Demos_report/FINAL_E_deformed/temperature_sensing/debug_fft_mag.png

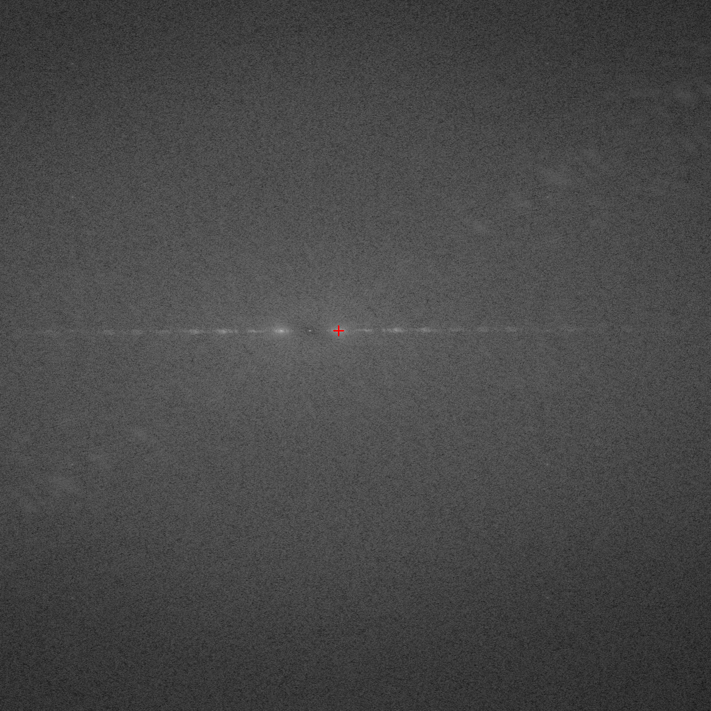
Multimodal_Sensor/Demos_report/FINAL_E_deformed/temperature_sensing/debug_fft_mag.png
