rimelq/VISTAF-RoboSkin-Vision-Integrated-Multimodal-Sensor/Multimodal_Sensor/Demos_report/FINAL_F_deformed/temperature_sensing/debug_color_raw_colormap_20_75.png

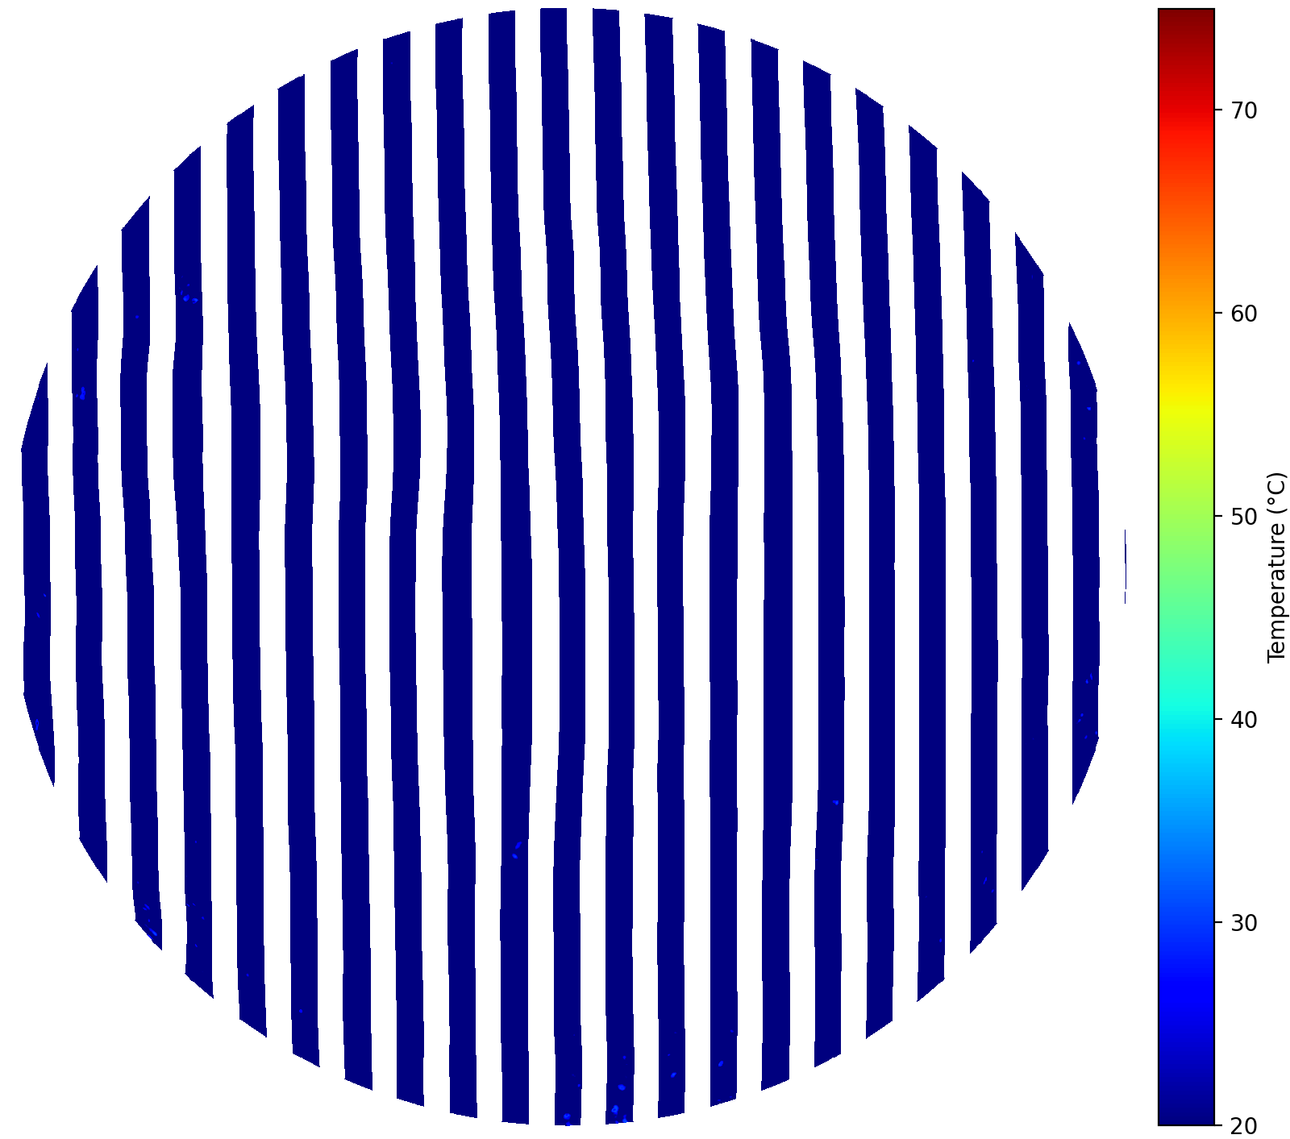
Multimodal_Sensor/Demos_report/FINAL_F_deformed/temperature_sensing/debug_color_raw_colormap_20_75.png
