rimelq/VISTAF-RoboSkin-Vision-Integrated-Multimodal-Sensor/Multimodal_Sensor/Demos_report/FINAL_P_deformed/temperature_sensing/debug_seg_overlay.png

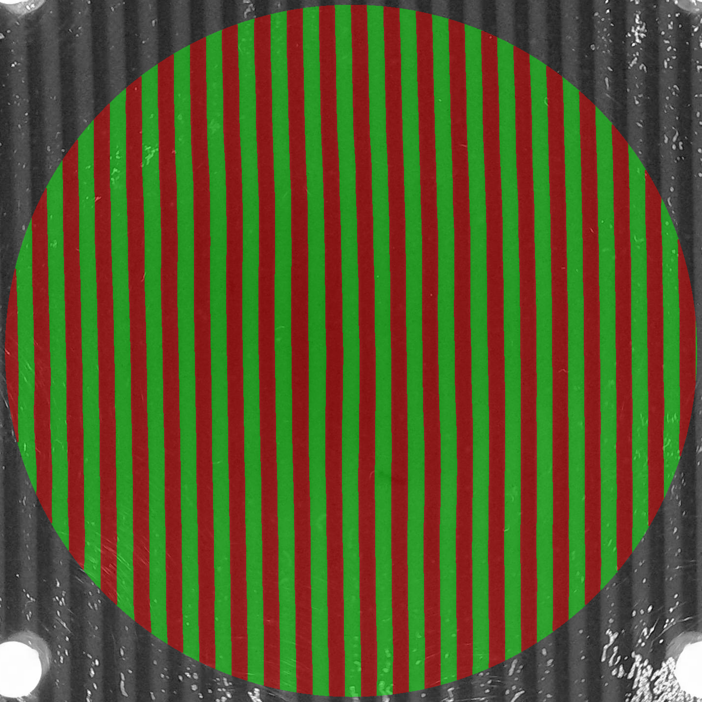
Multimodal_Sensor/Demos_report/FINAL_P_deformed/temperature_sensing/debug_seg_overlay.png
