rimelq/VISTAF-RoboSkin-Vision-Integrated-Multimodal-Sensor/Multimodal_Sensor/Demos_report/FINAL_ROUND_METAL/force_sensing/ftp_run/DEBUG_ramp_cross_phase_diff.png

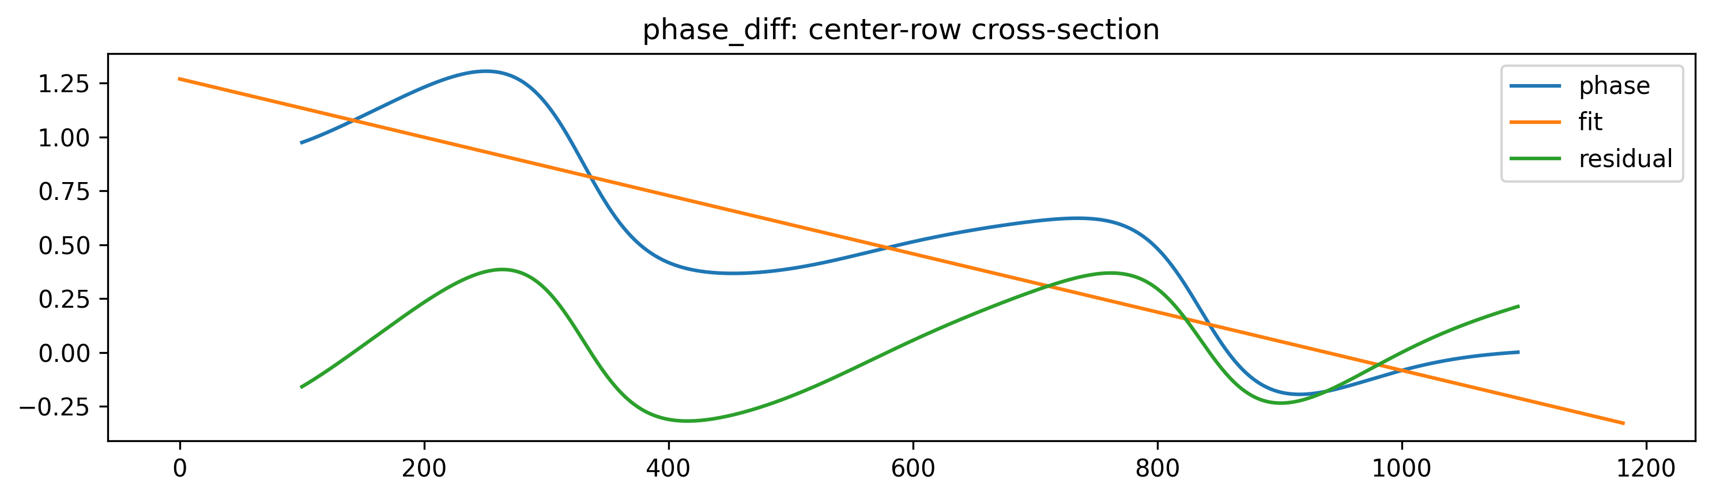
Multimodal_Sensor/Demos_report/FINAL_ROUND_METAL/force_sensing/ftp_run/DEBUG_ramp_cross_phase_diff.png
