rimelq/VISTAF-RoboSkin-Vision-Integrated-Multimodal-Sensor/Multimodal_Sensor/Demos_report/FINAL_ROUND_METAL/temperature_sensing/debug_chroma_u8.png

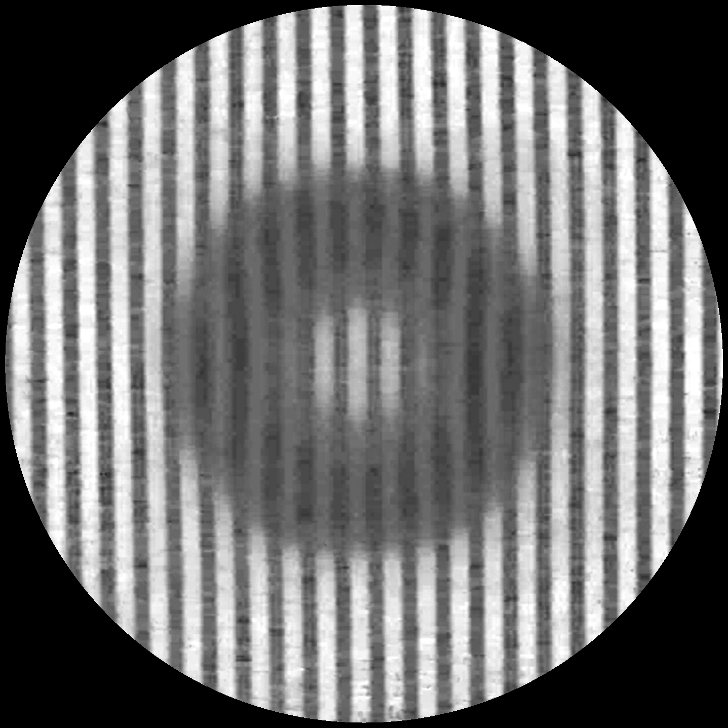
Multimodal_Sensor/Demos_report/FINAL_ROUND_METAL/temperature_sensing/debug_chroma_u8.png
