rimelq/VISTAF-RoboSkin-Vision-Integrated-Multimodal-Sensor/Multimodal_Sensor/Demos_report/FINAL_ROUND_METAL/temperature_sensing/debug_wide_raw_light_only_colormap.png

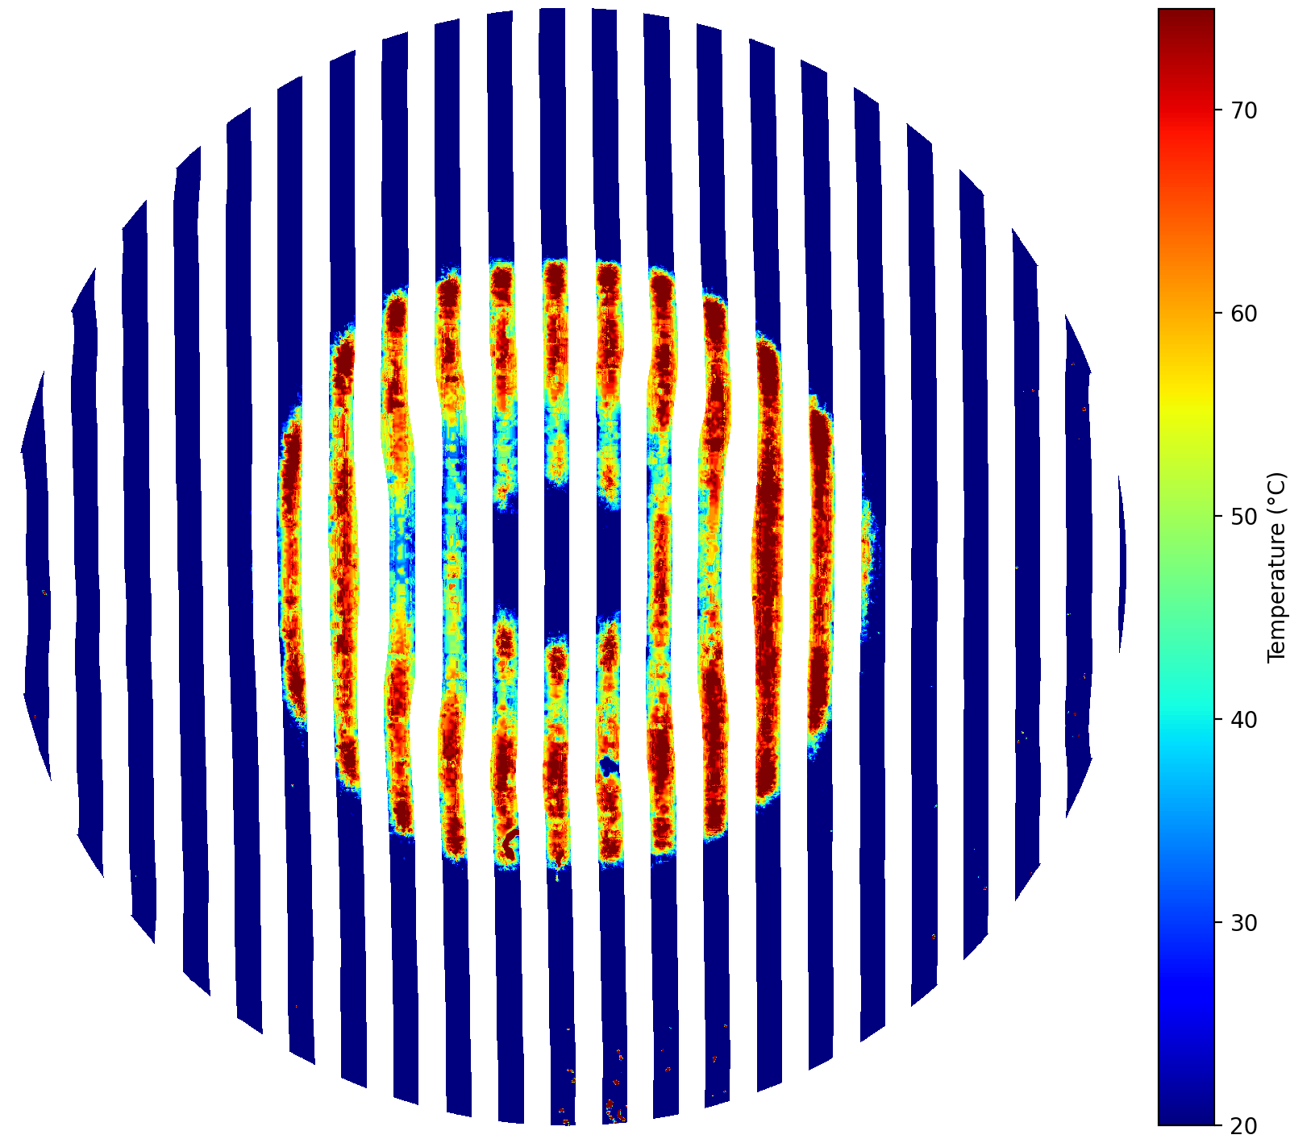
Multimodal_Sensor/Demos_report/FINAL_ROUND_METAL/temperature_sensing/debug_wide_raw_light_only_colormap.png
