rimelq/VISTAF-RoboSkin-Vision-Integrated-Multimodal-Sensor/Multimodal_Sensor/Demos_report/FINAL_TEMP_DEMO/force_sensing/ftp_run/DEBUG_ramp_phase_diff.png

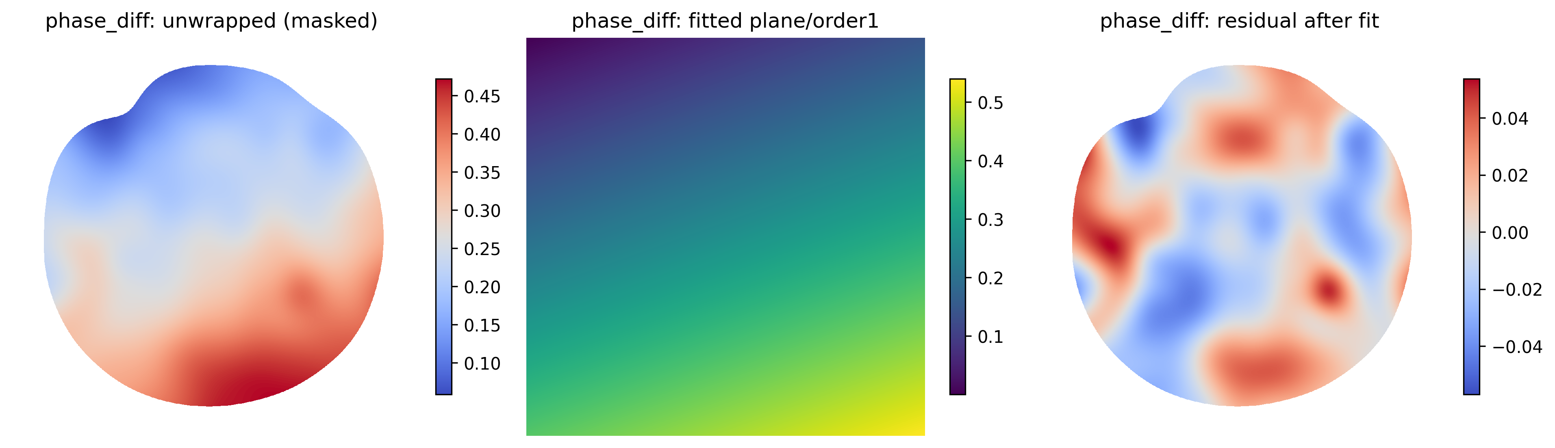
Multimodal_Sensor/Demos_report/FINAL_TEMP_DEMO/force_sensing/ftp_run/DEBUG_ramp_phase_diff.png
