rimelq/VISTAF-RoboSkin-Vision-Integrated-Multimodal-Sensor/Multimodal_Sensor/Demos_report/FINAL_TEMP_DEMO/temperature_sensing/debug_chroma_u8.png

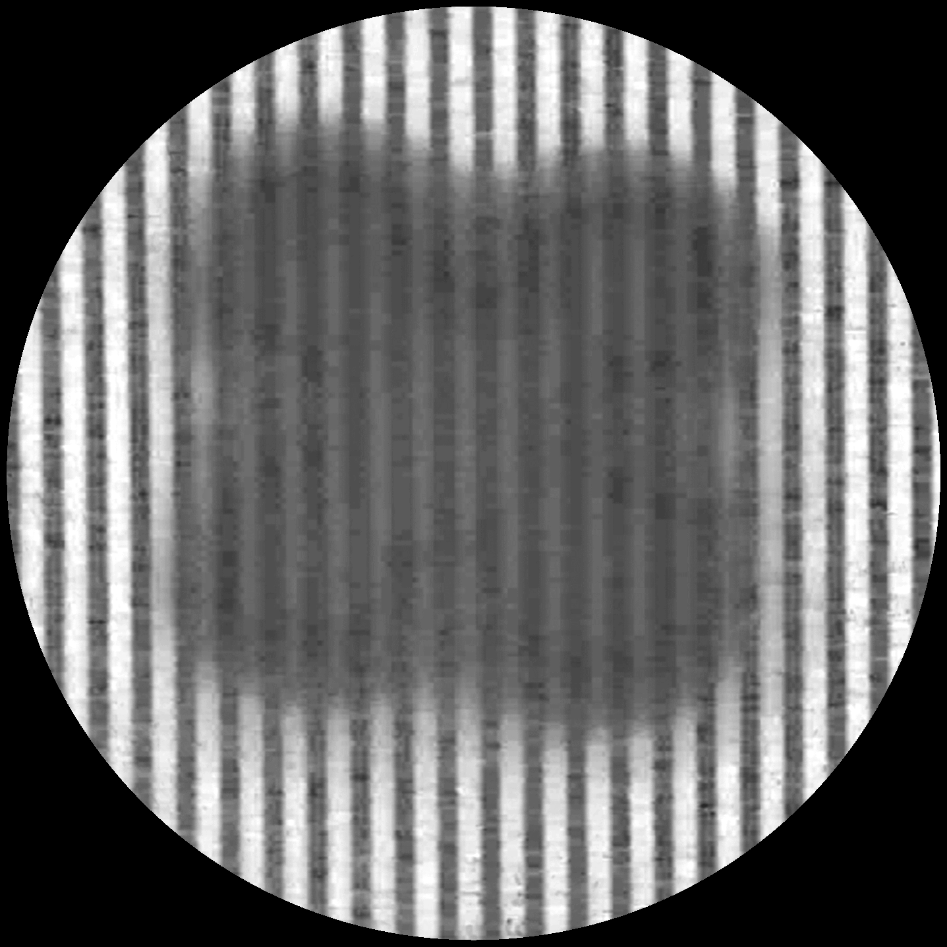
Multimodal_Sensor/Demos_report/FINAL_TEMP_DEMO/temperature_sensing/debug_chroma_u8.png
